aggerritsen/VespaSmartTrap-BASE/docs/hardware/Grove-Vision-AI-Module-V2-functions.jpg

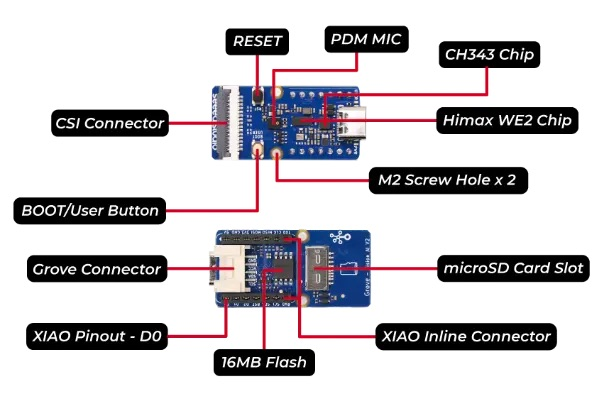
docs/hardware/Grove-Vision-AI-Module-V2-functions.jpg
