aggerritsen/VespaSmartTrap-BASE/tools/data/power_uptime_plot.png

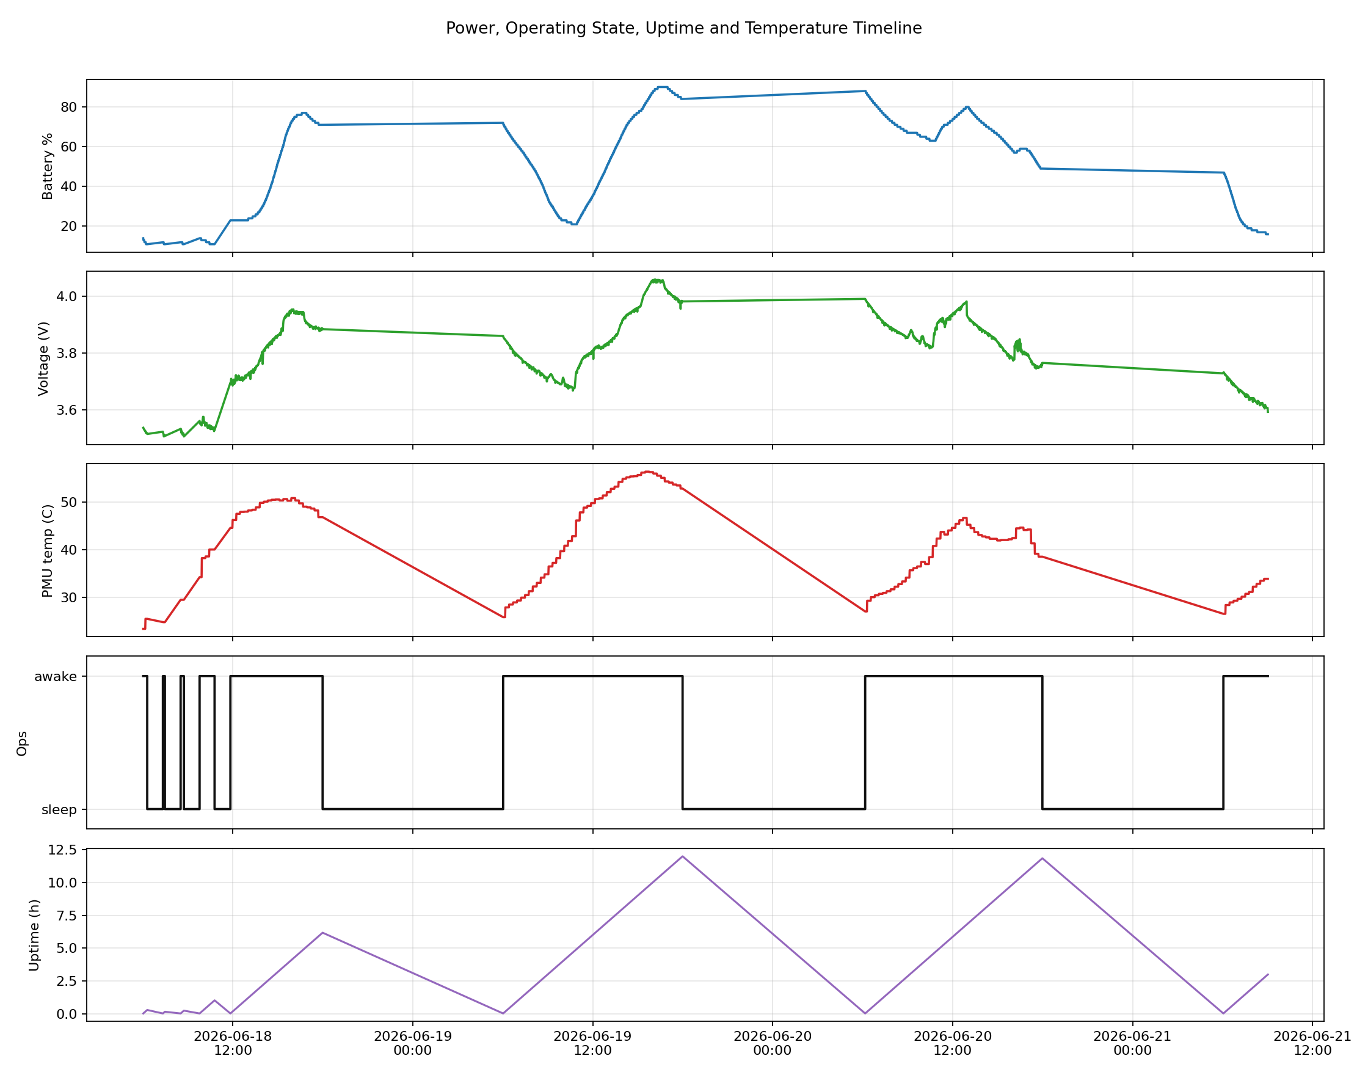
tools/data/power_uptime_plot.png
