aggerritsen/VespaSmartTrap-BASE/tools/image-viewer/images/ApisMellifera/111432916.jpg

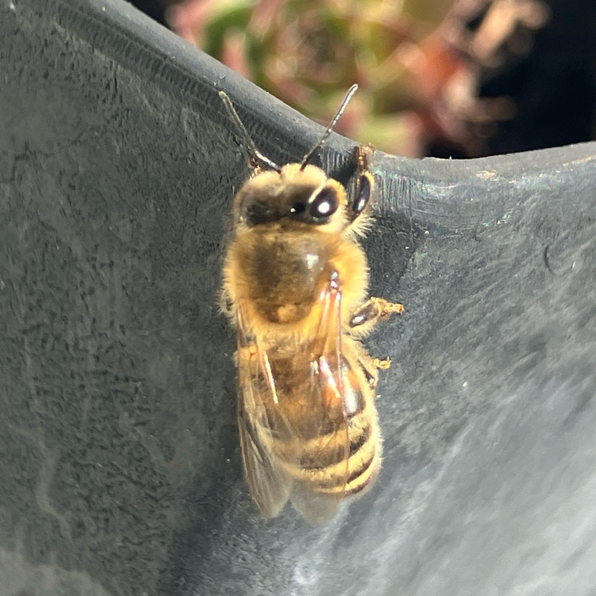
tools/image-viewer/images/ApisMellifera/111432916.jpg
