aggerritsen/VespaSmartTrap-BASE/tools/image-viewer/images/ApisMellifera/111468807.jpg

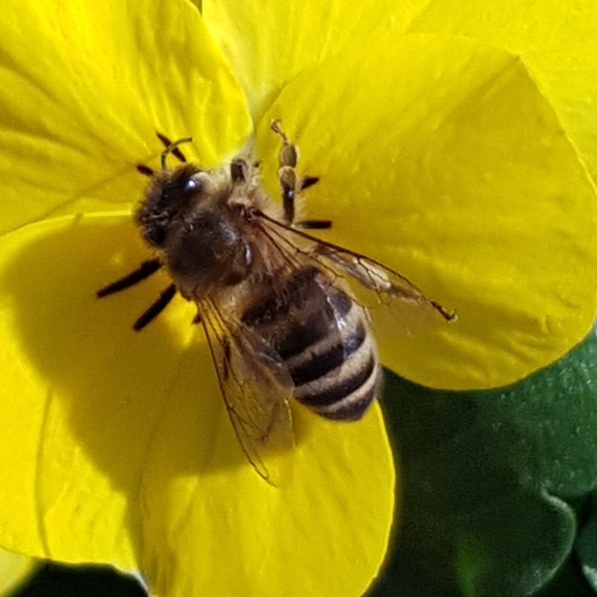
tools/image-viewer/images/ApisMellifera/111468807.jpg
