aggerritsen/VespaSmartTrap-BASE/tools/image-viewer/images/ApisMellifera/111469478.jpg

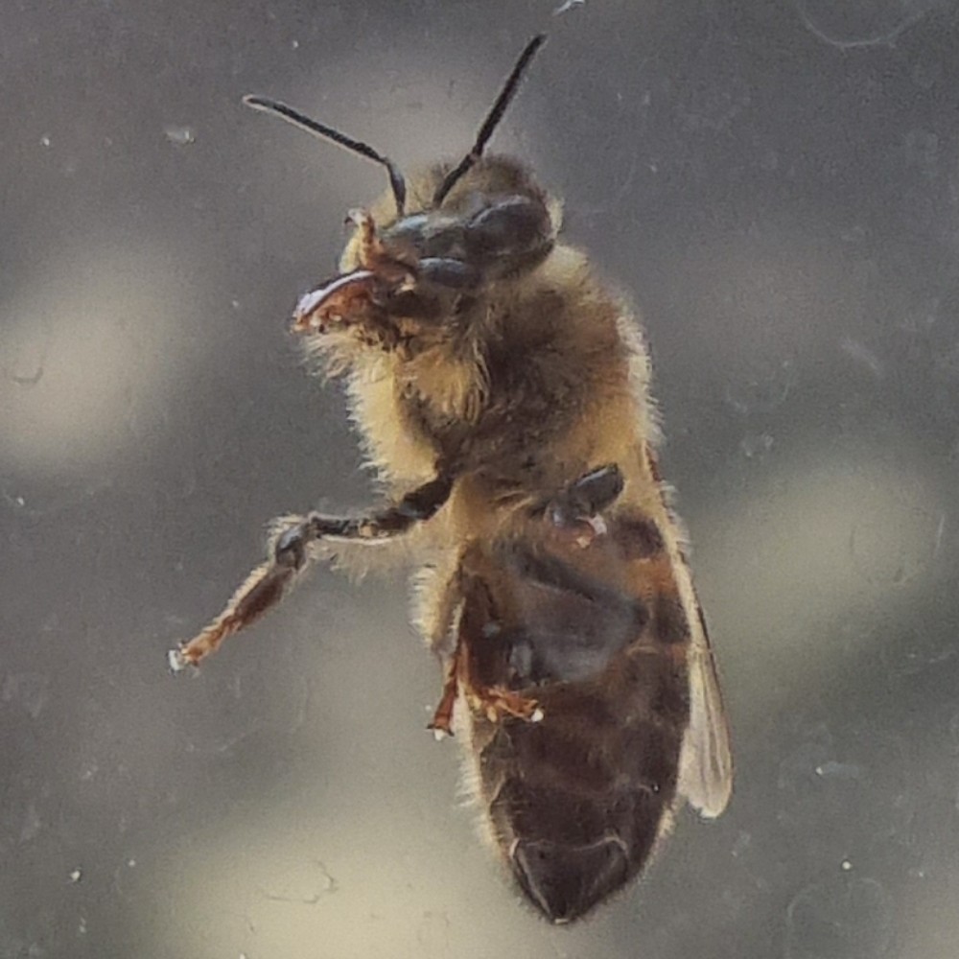
tools/image-viewer/images/ApisMellifera/111469478.jpg
