aggerritsen/VespaSmartTrap-BASE/tools/image-viewer/images/ApisMellifera/111470358.jpg

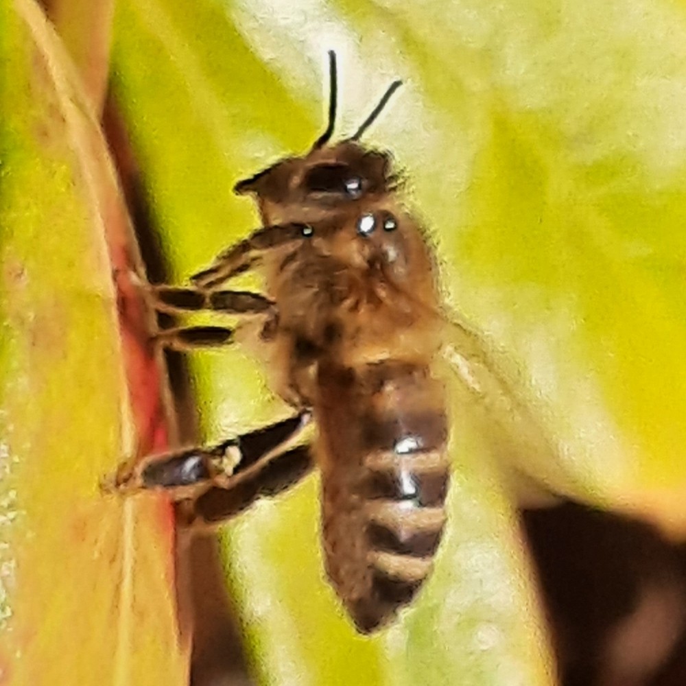
tools/image-viewer/images/ApisMellifera/111470358.jpg
