aggerritsen/VespaSmartTrap-BASE/tools/image-viewer/images/ApisMellifera/111476436.jpg

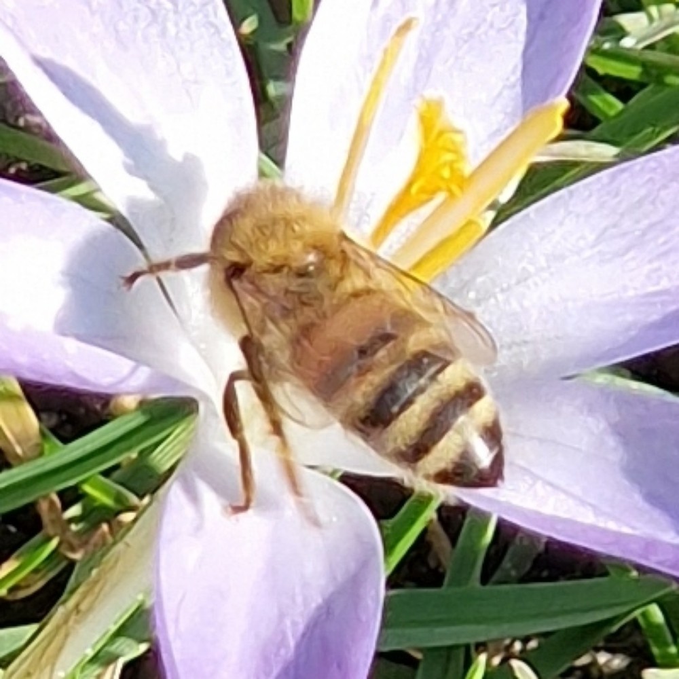
tools/image-viewer/images/ApisMellifera/111476436.jpg
