aggerritsen/VespaSmartTrap-BASE/tools/image-viewer/images/ApisMellifera/111476663.jpg

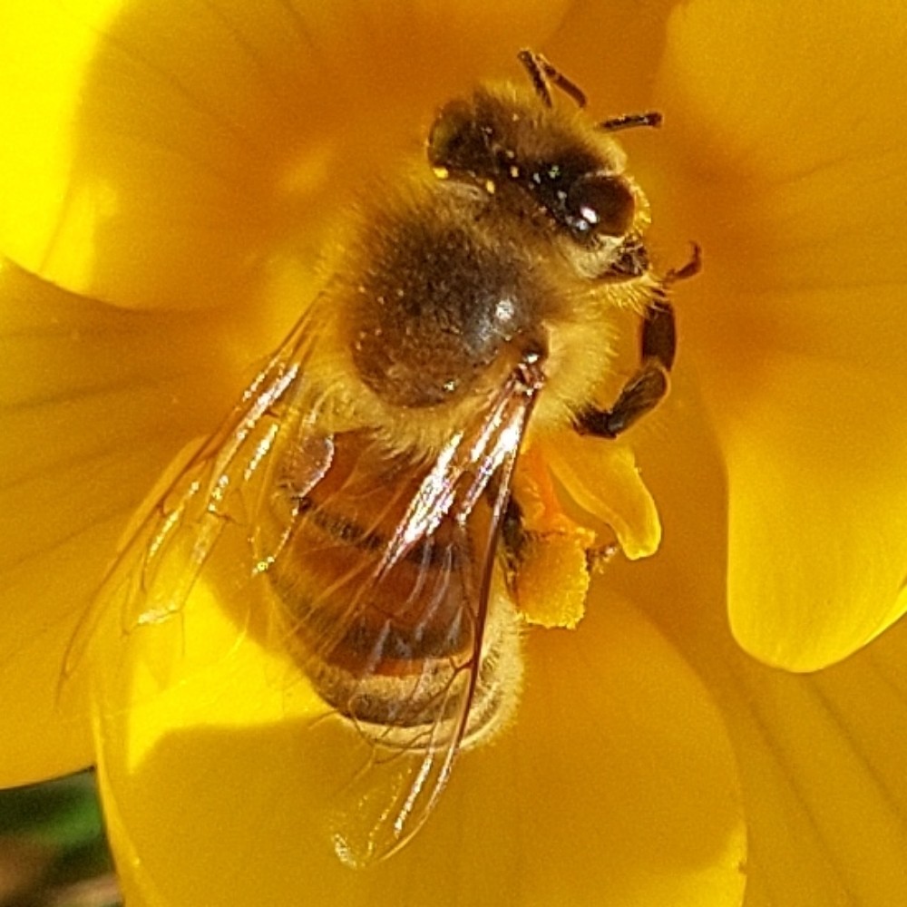
tools/image-viewer/images/ApisMellifera/111476663.jpg
