aggerritsen/VespaSmartTrap-BASE/tools/image-viewer/images/ApisMellifera/111479601.jpg

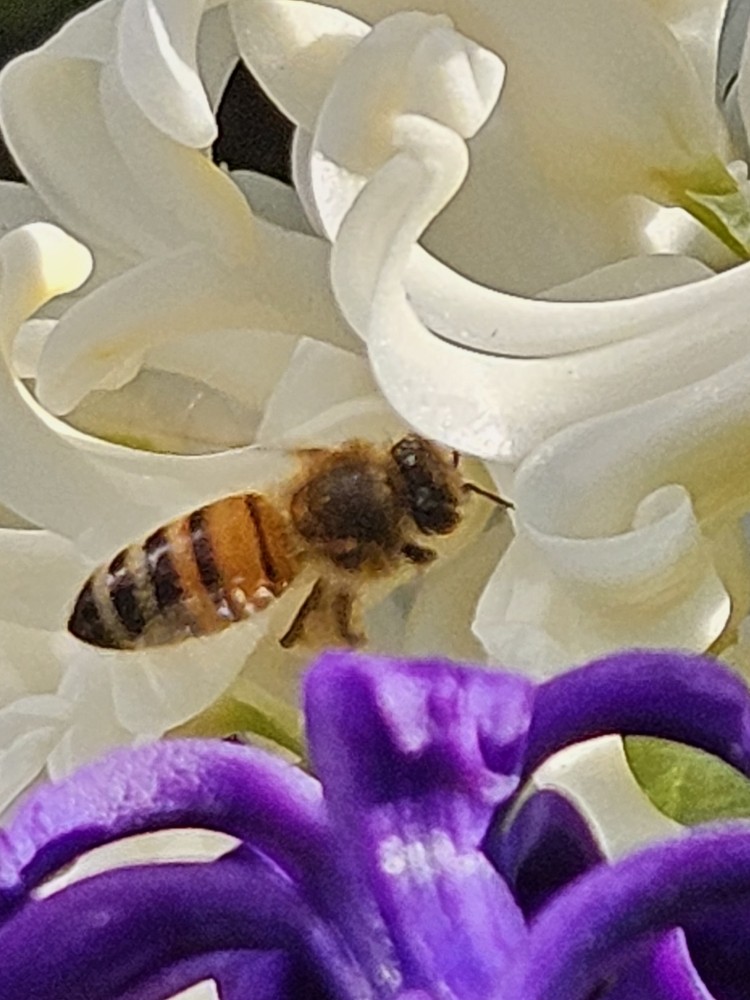
tools/image-viewer/images/ApisMellifera/111479601.jpg
