aggerritsen/VespaSmartTrap-BASE/tools/image-viewer/images/ApisMellifera/111512250.jpg

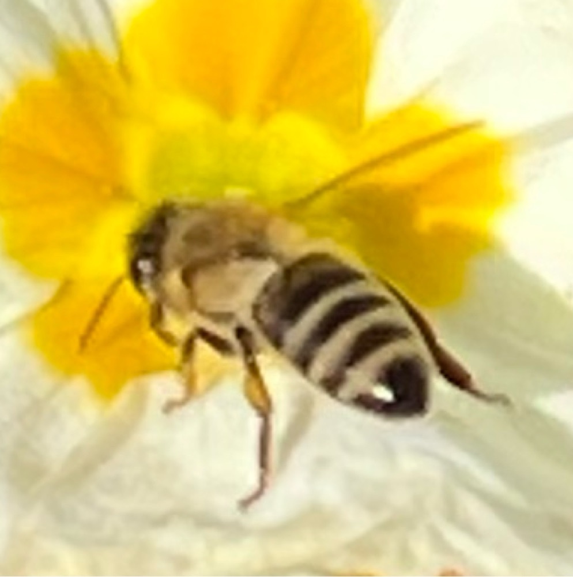
tools/image-viewer/images/ApisMellifera/111512250.jpg
