aggerritsen/VespaSmartTrap-BASE/tools/image-viewer/images/ApisMellifera/111513801.jpg

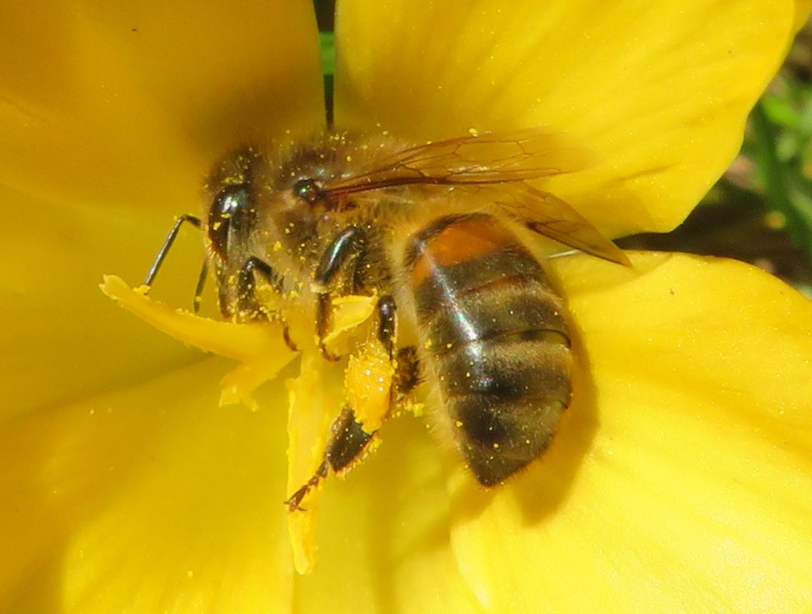
tools/image-viewer/images/ApisMellifera/111513801.jpg
