aggerritsen/VespaSmartTrap-BASE/tools/image-viewer/images/ApisMellifera/112025570.jpg

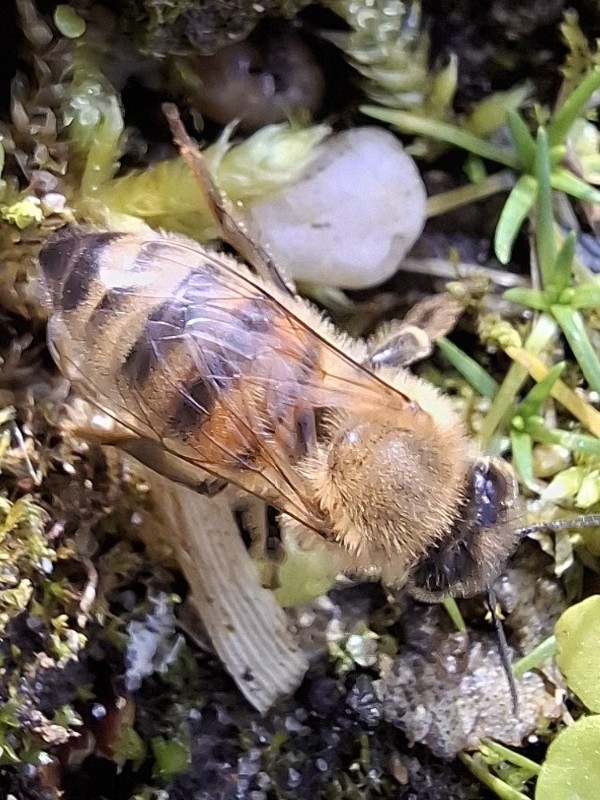
tools/image-viewer/images/ApisMellifera/112025570.jpg
