aggerritsen/VespaSmartTrap-BASE/tools/image-viewer/images/VespaCabro/111761089.jpg

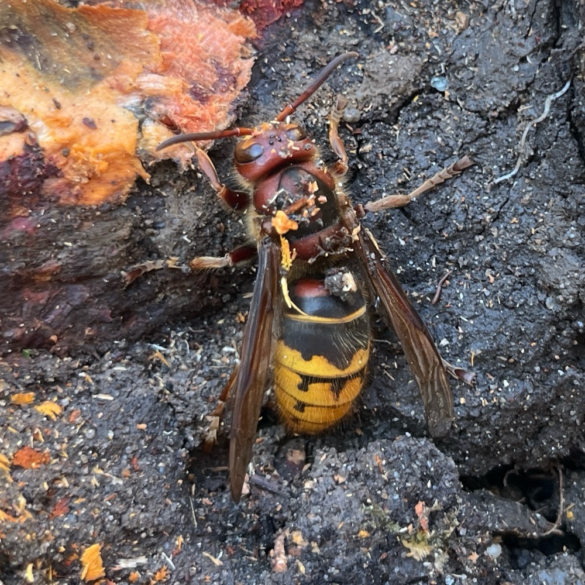
tools/image-viewer/images/VespaCabro/111761089.jpg
