aggerritsen/VespaSmartTrap-BASE/tools/image-viewer/images/VespaCabro/112134146.jpg

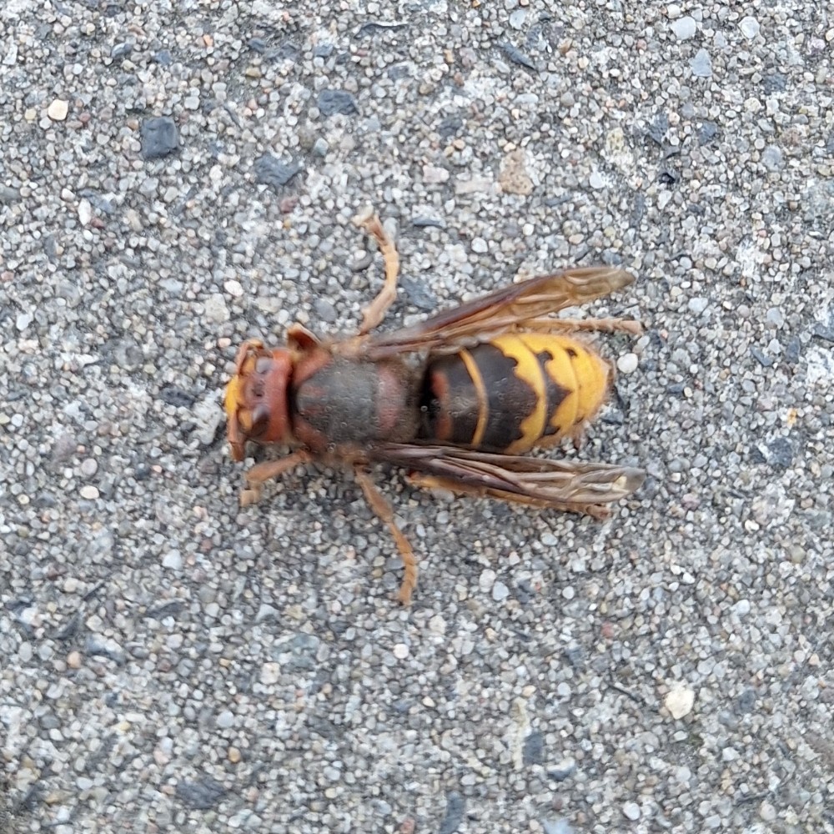
tools/image-viewer/images/VespaCabro/112134146.jpg
