aggerritsen/VespaSmartTrap-BASE/tools/image-viewer/images/VespaCabro/112459961.jpg

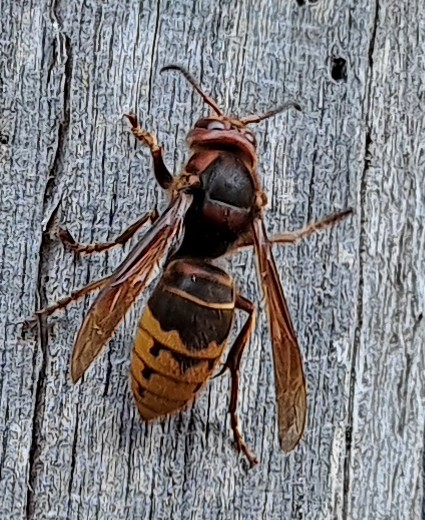
tools/image-viewer/images/VespaCabro/112459961.jpg
