aggerritsen/VespaSmartTrap-BASE/tools/image-viewer/images/VespaCabro/112593887.jpg

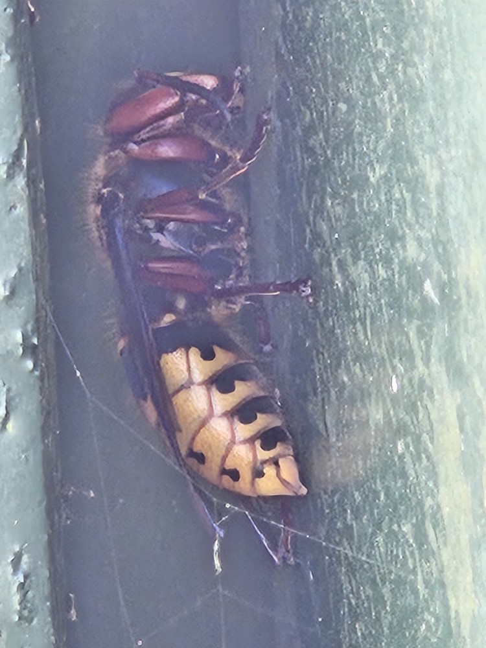
tools/image-viewer/images/VespaCabro/112593887.jpg
