aggerritsen/VespaSmartTrap-BASE/tools/image-viewer/images/VespaCabro/112712739.jpg

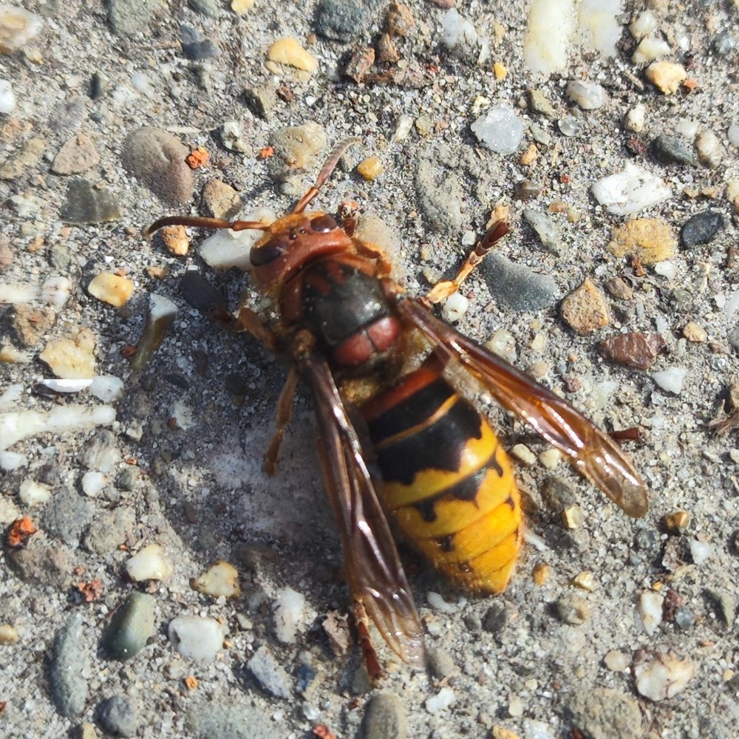
tools/image-viewer/images/VespaCabro/112712739.jpg
