aggerritsen/VespaSmartTrap-BASE/tools/image-viewer/images/VespaCabro/112884580.jpg

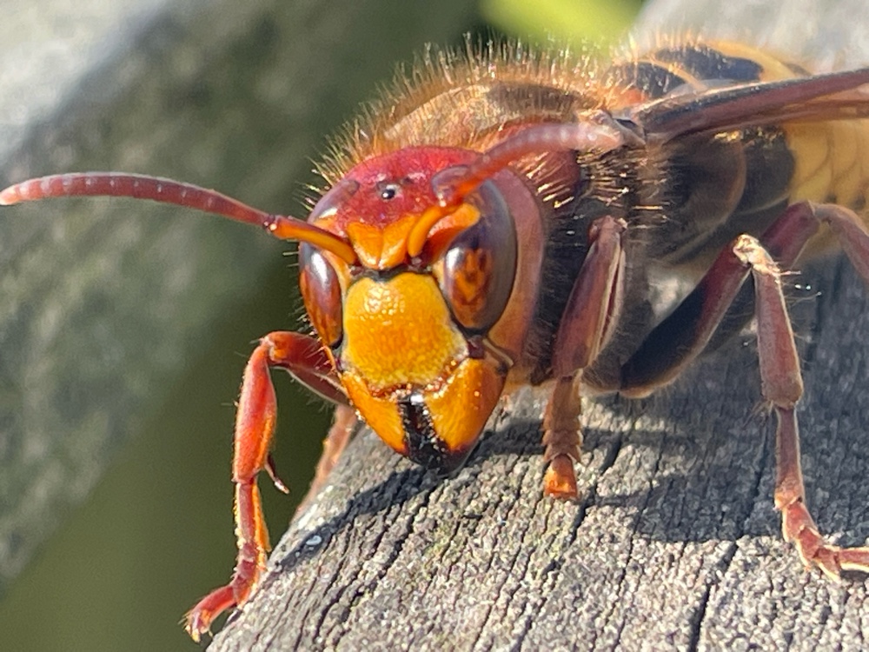
tools/image-viewer/images/VespaCabro/112884580.jpg
