aggerritsen/VespaSmartTrap-BASE/tools/image-viewer/images/VespaCabro/112900468.jpg

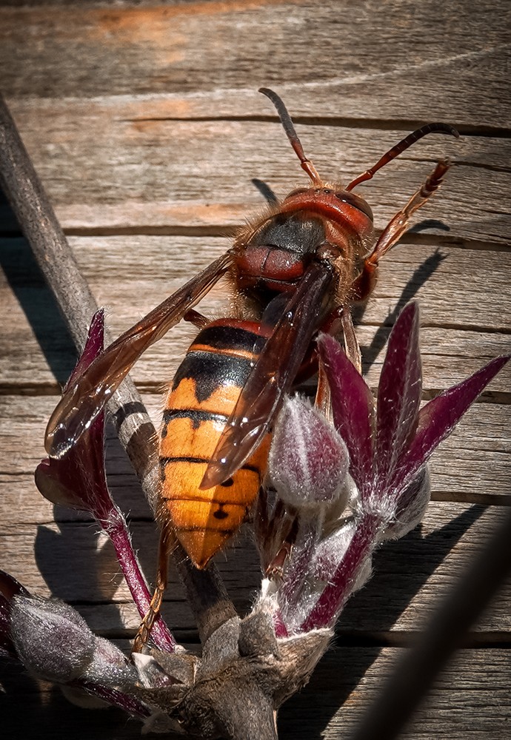
tools/image-viewer/images/VespaCabro/112900468.jpg
