aggerritsen/VespaSmartTrap-BASE/tools/image-viewer/images/VespaCabro/112967960.jpg

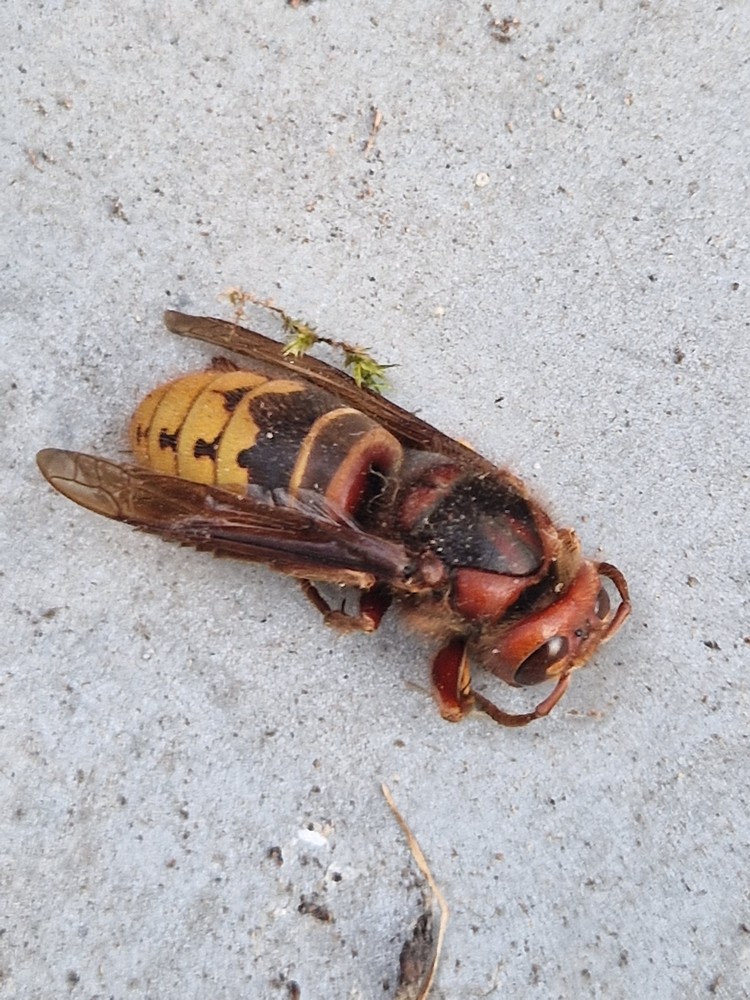
tools/image-viewer/images/VespaCabro/112967960.jpg
