aggerritsen/VespaSmartTrap-BASE/tools/image-viewer/images/VespaCabro/113068991.jpg

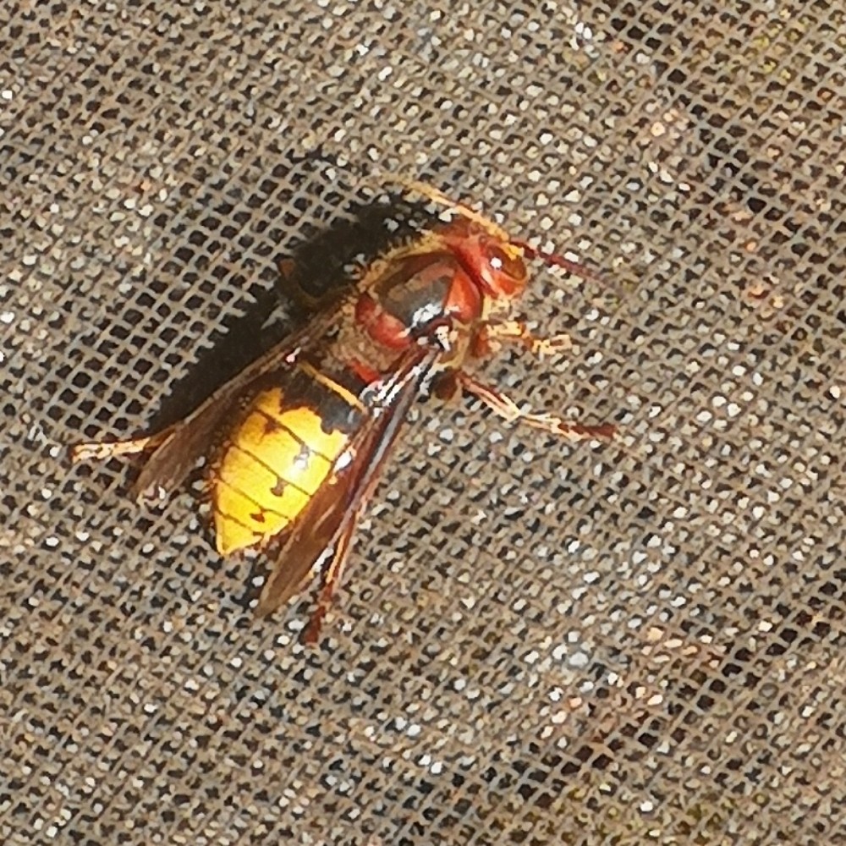
tools/image-viewer/images/VespaCabro/113068991.jpg
