aggerritsen/VespaSmartTrap-BASE/tools/image-viewer/images/VespaVelutina/112178689.jpg

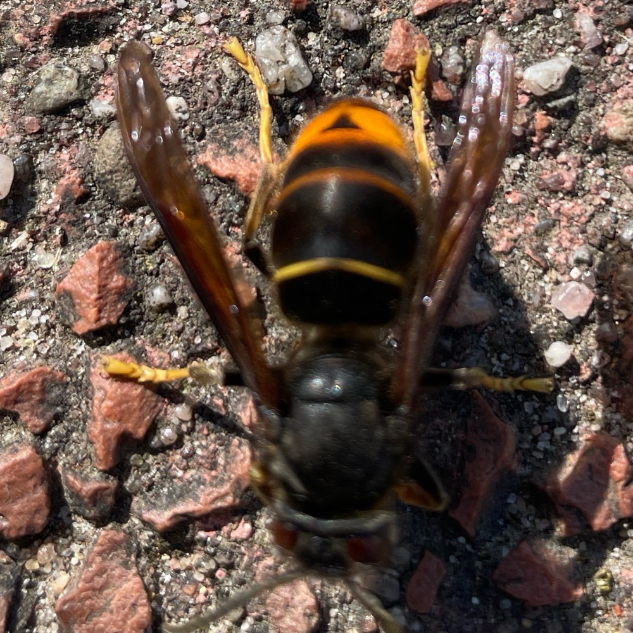
tools/image-viewer/images/VespaVelutina/112178689.jpg
