aggerritsen/VespaSmartTrap-BASE/tools/image-viewer/images/VespaVelutina/112180438.jpg

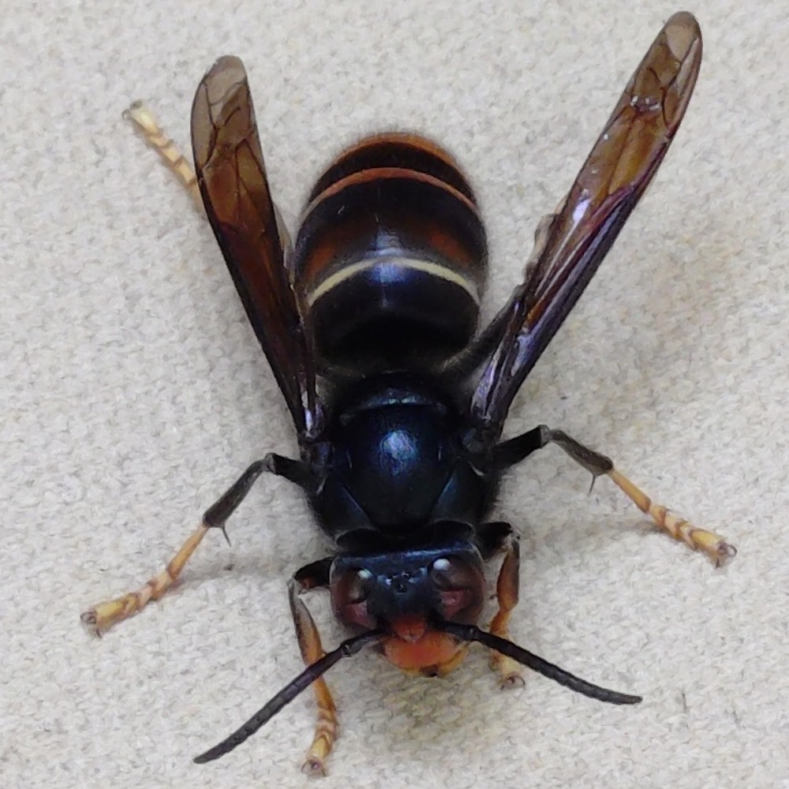
tools/image-viewer/images/VespaVelutina/112180438.jpg
