aggerritsen/VespaSmartTrap-BASE/tools/image-viewer/images/VespaVelutina/112218984.jpg

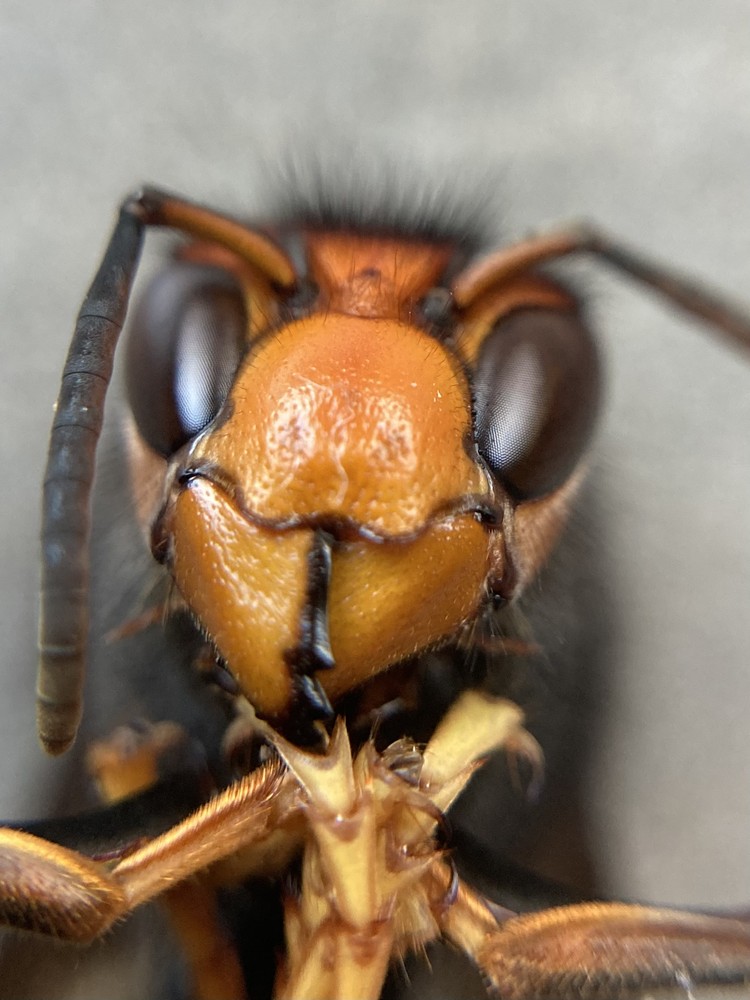
tools/image-viewer/images/VespaVelutina/112218984.jpg
