aggerritsen/VespaSmartTrap-BASE/tools/image-viewer/images/VespaVelutina/112255665.jpg

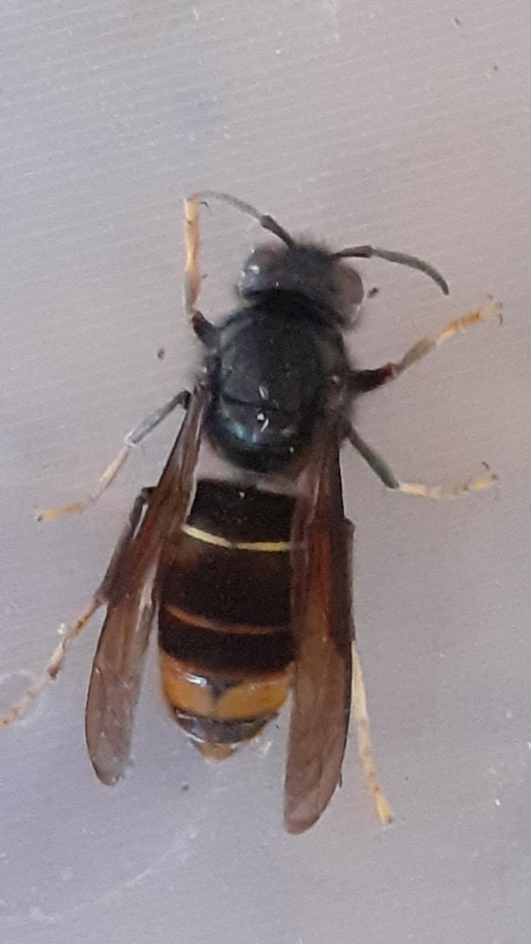
tools/image-viewer/images/VespaVelutina/112255665.jpg
