aggerritsen/VespaSmartTrap-BASE/tools/image-viewer/images/VespaVelutina/113046975.jpg

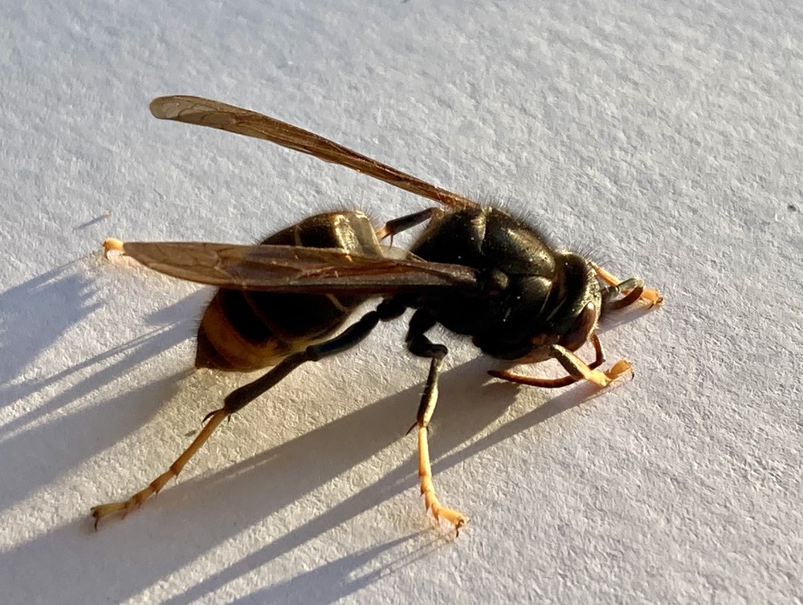
tools/image-viewer/images/VespaVelutina/113046975.jpg
