aggerritsen/VespaSmartTrap-BASE/tools/image-viewer/images/VespaVelutina/113052811.jpg

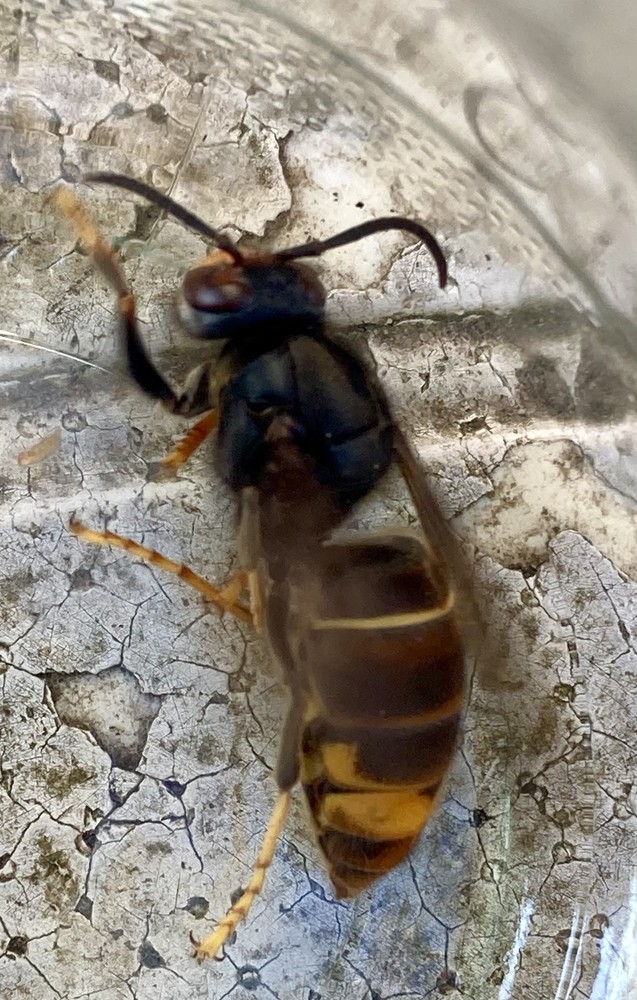
tools/image-viewer/images/VespaVelutina/113052811.jpg
