aggerritsen/VespaSmartTrap-BASE/tools/image-viewer/images/VespaVelutina/113054008.jpg

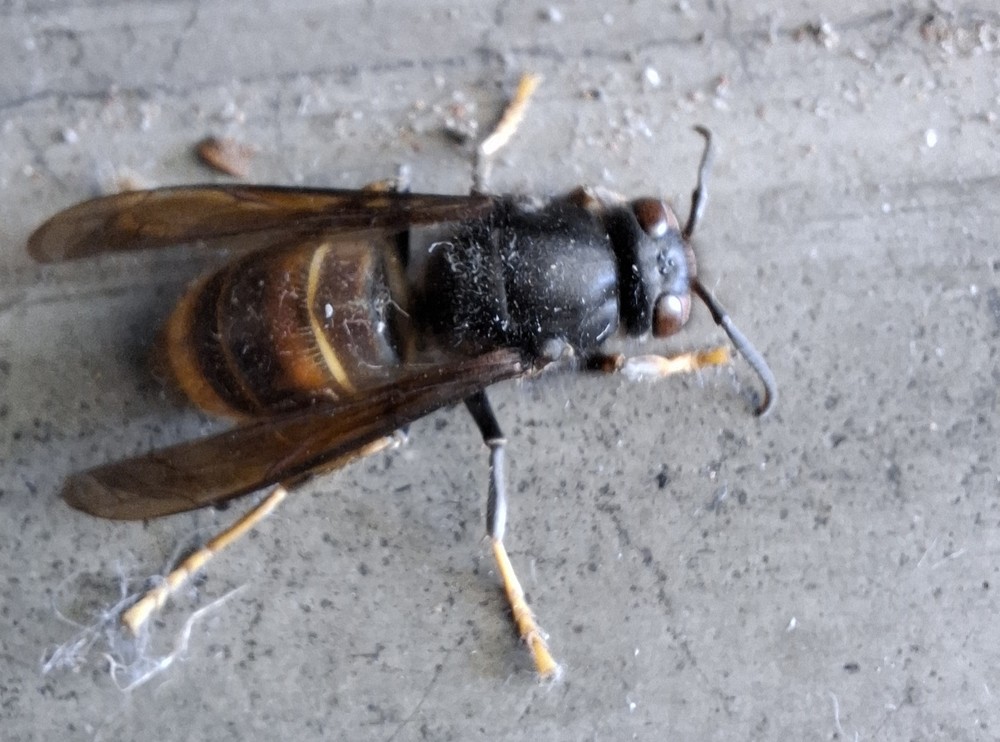
tools/image-viewer/images/VespaVelutina/113054008.jpg
