aggerritsen/VespaSmartTrap-BASE/tools/image-viewer/images/VespaVelutina/113058650.jpg

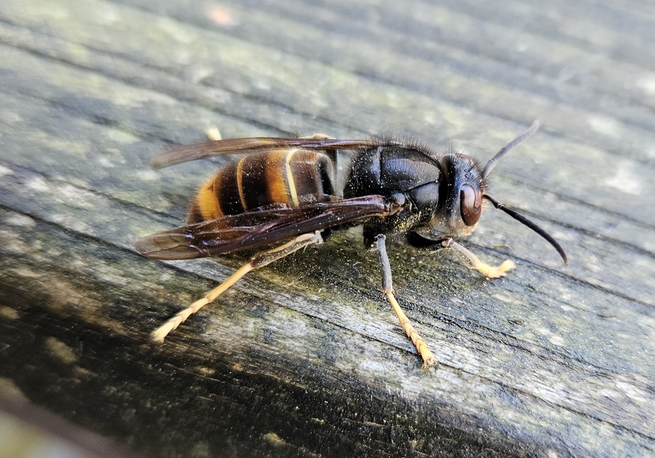
tools/image-viewer/images/VespaVelutina/113058650.jpg
