aggerritsen/VespaSmartTrap-BASE/tools/image-viewer/images/VespaVelutina/113204112.jpg

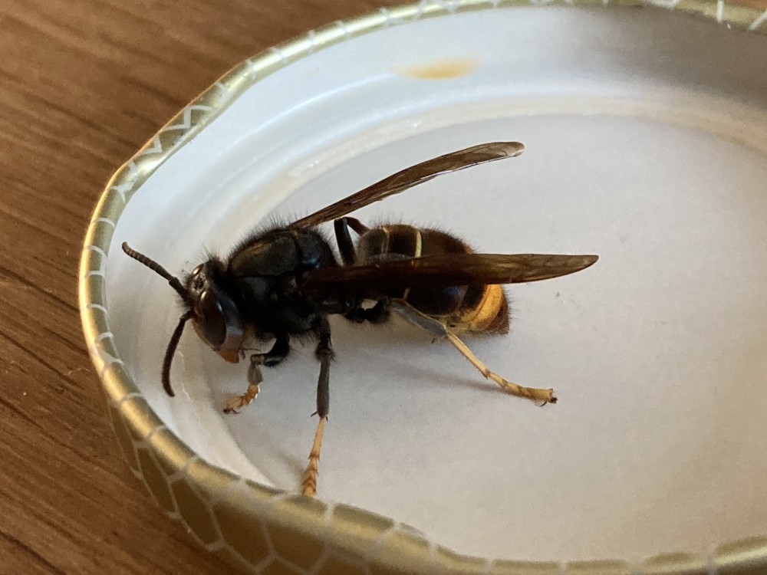
tools/image-viewer/images/VespaVelutina/113204112.jpg
