aggerritsen/VespaSmartTrap-BASE/tools/image-viewer/images/VespaVelutina/113204113.jpg

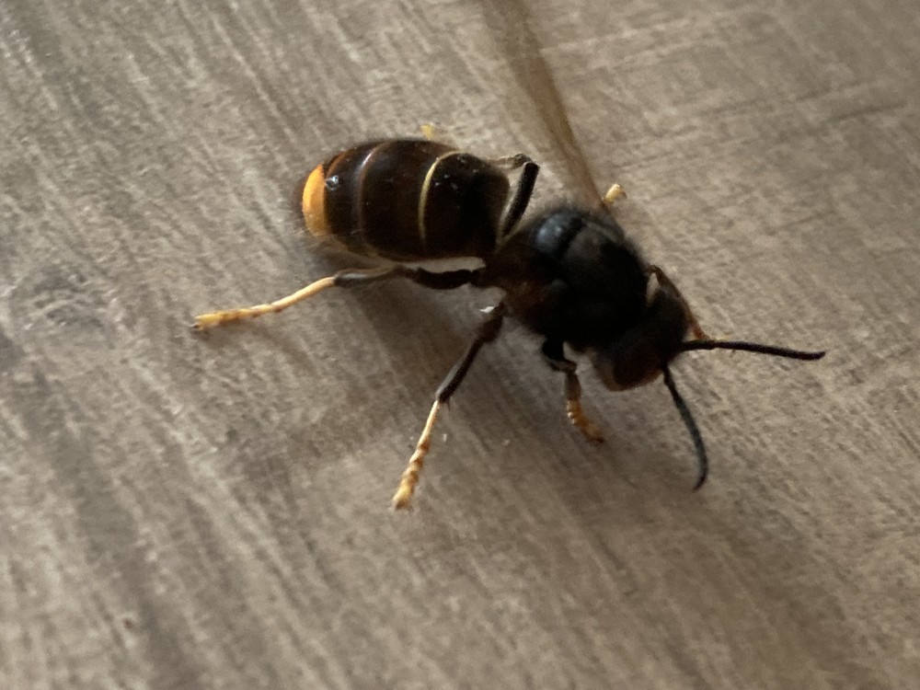
tools/image-viewer/images/VespaVelutina/113204113.jpg
