aggerritsen/VespaSmartTrap-BASE/tools/image-viewer/images/VespaVelutina/141795838.jpg

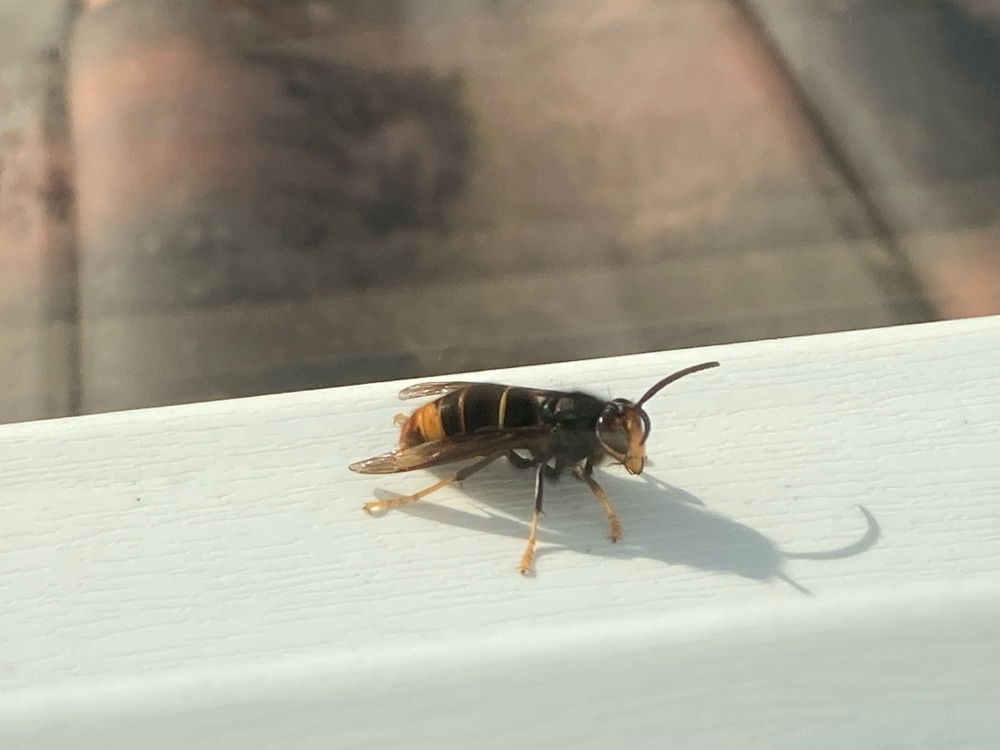
tools/image-viewer/images/VespaVelutina/141795838.jpg
