aggerritsen/VespaSmartTrap-BASE/tools/image-viewer/images/VespaVelutina/141813378.jpg

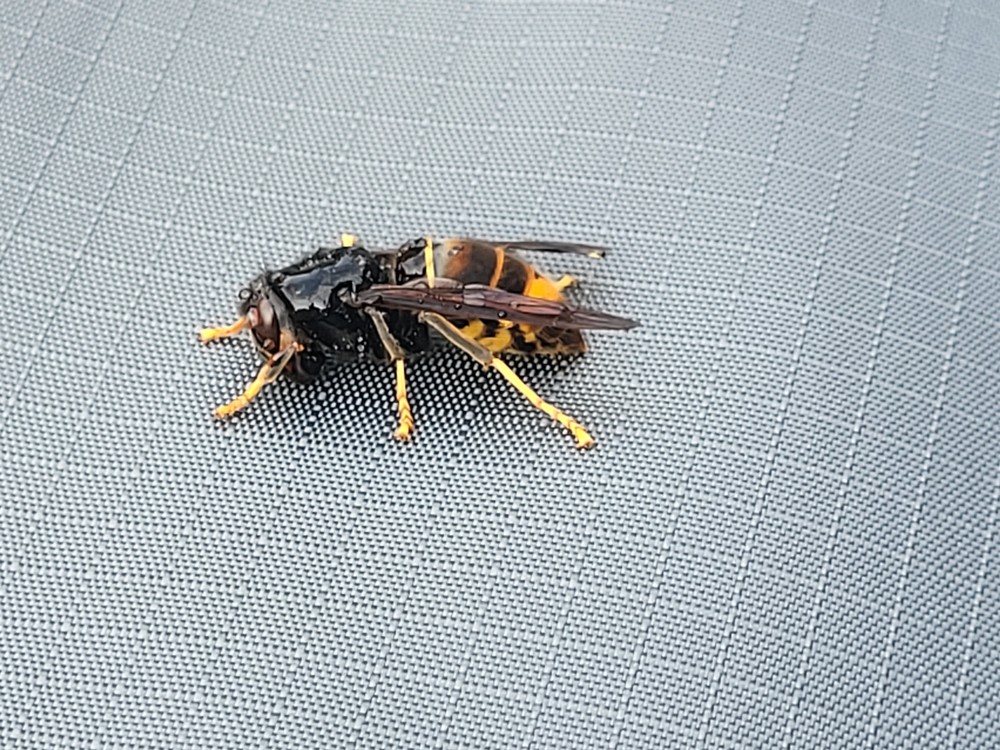
tools/image-viewer/images/VespaVelutina/141813378.jpg
