aggerritsen/VespaSmartTrap-BASE/tools/image-viewer/images/VespaVelutina/141822580 (1).jpg

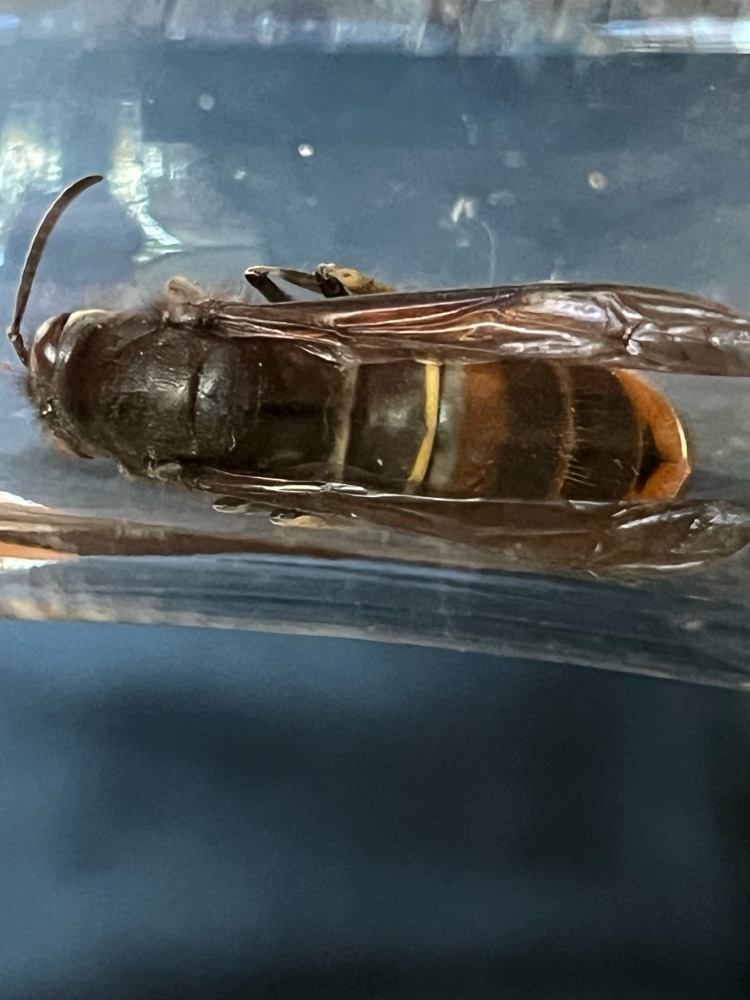
tools/image-viewer/images/VespaVelutina/141822580 (1).jpg
