aggerritsen/VespaSmartTrap-BASE/tools/image-viewer/images/VespaVelutina/141822581.jpg

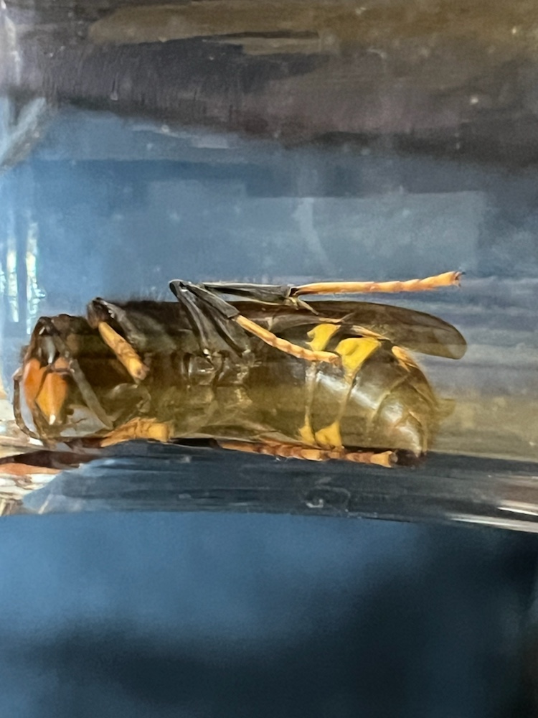
tools/image-viewer/images/VespaVelutina/141822581.jpg
