aggerritsen/VespaSmartTrap-BASE/tools/image-viewer/images/VespaVelutina/141857367.jpg

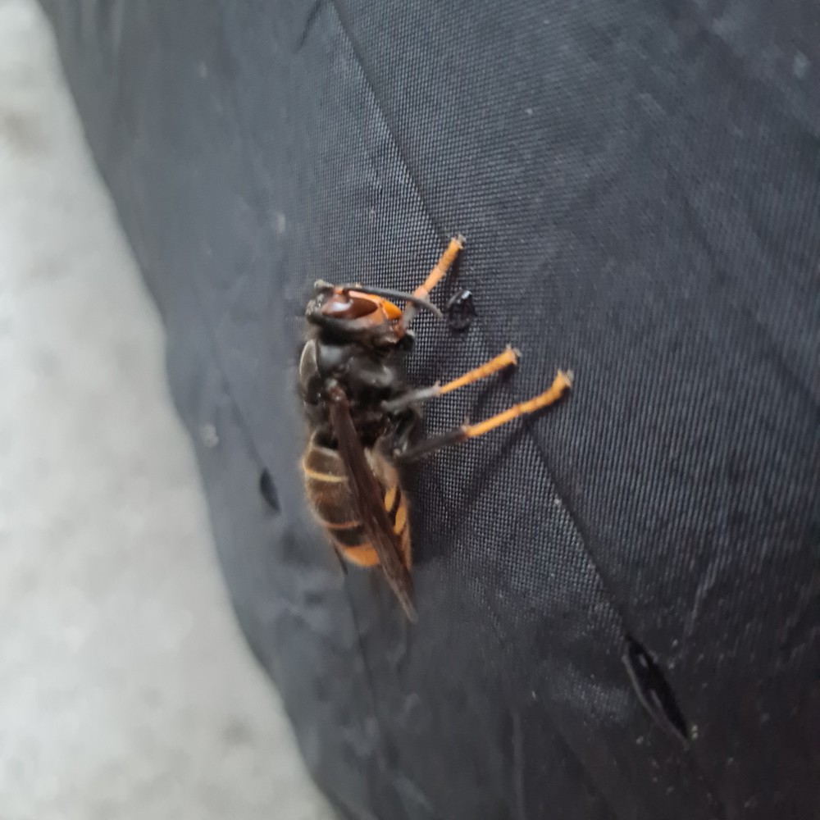
tools/image-viewer/images/VespaVelutina/141857367.jpg
