aggerritsen/VespaSmartTrap-BASE/tools/image-viewer/images/VespaVelutina/141879811.jpg

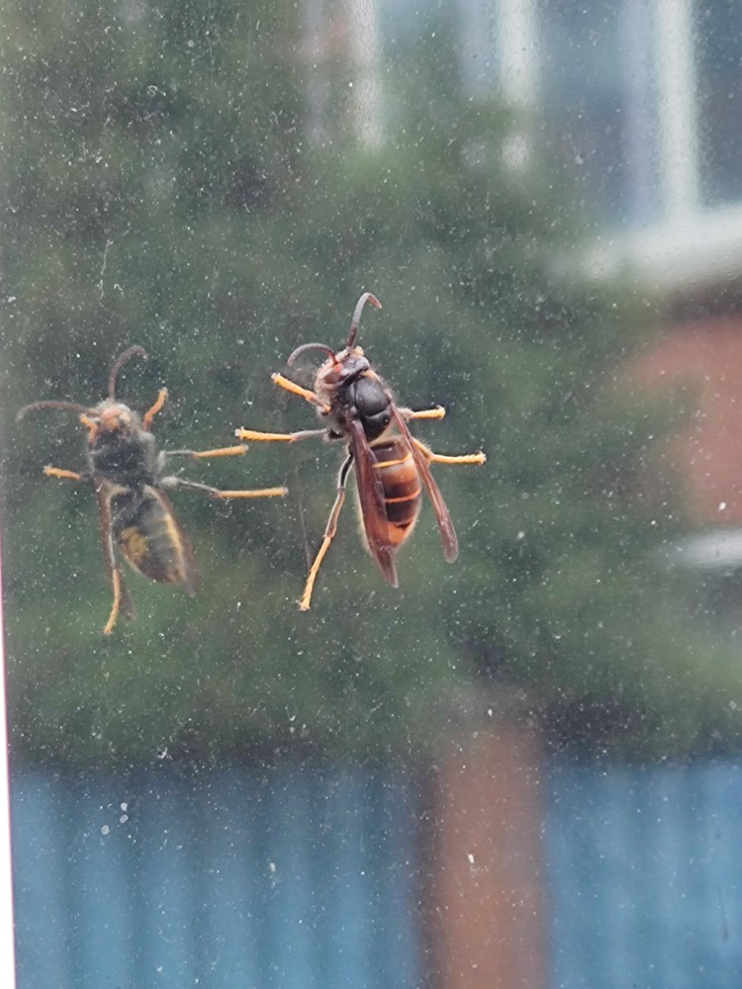
tools/image-viewer/images/VespaVelutina/141879811.jpg
