aggerritsen/VespaSmartTrap-BASE/tools/image-viewer/images/VespaVelutina/141879851 (1).jpg

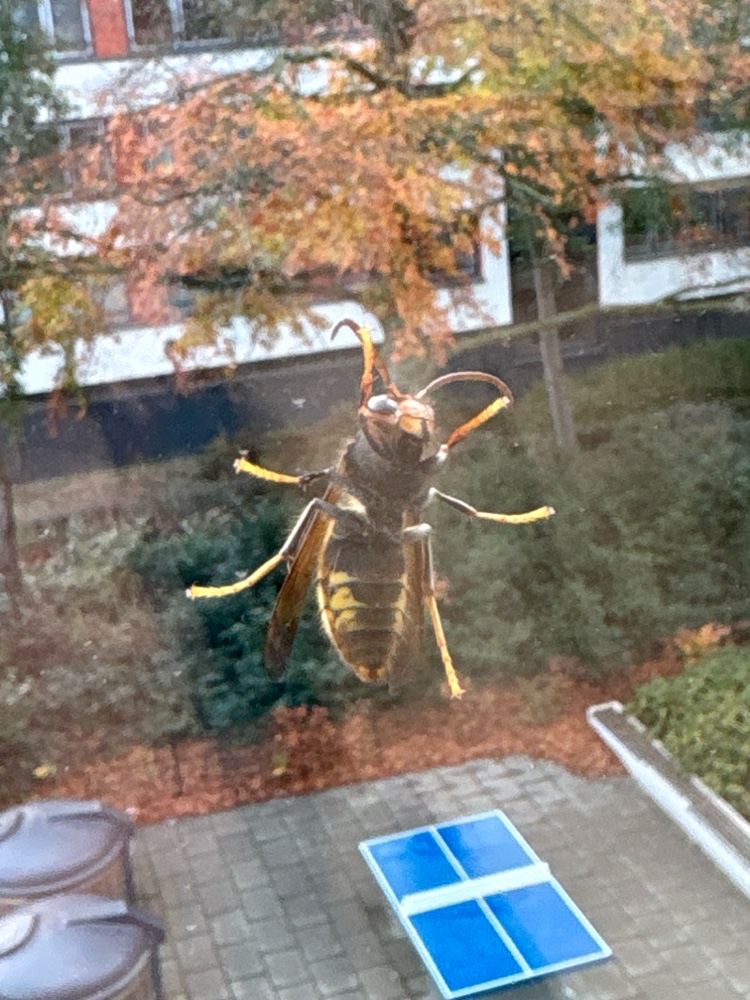
tools/image-viewer/images/VespaVelutina/141879851 (1).jpg
