aggerritsen/VespaSmartTrap-BASE/tools/image-viewer/images/VespaVelutina/141898289.jpg

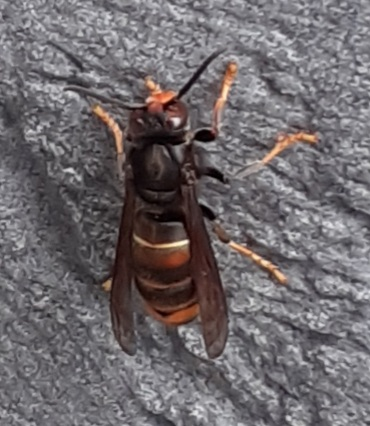
tools/image-viewer/images/VespaVelutina/141898289.jpg
