aggerritsen/VespaSmartTrap-BASE/tools/image-viewer/images/VespaVelutina/141899238.jpg

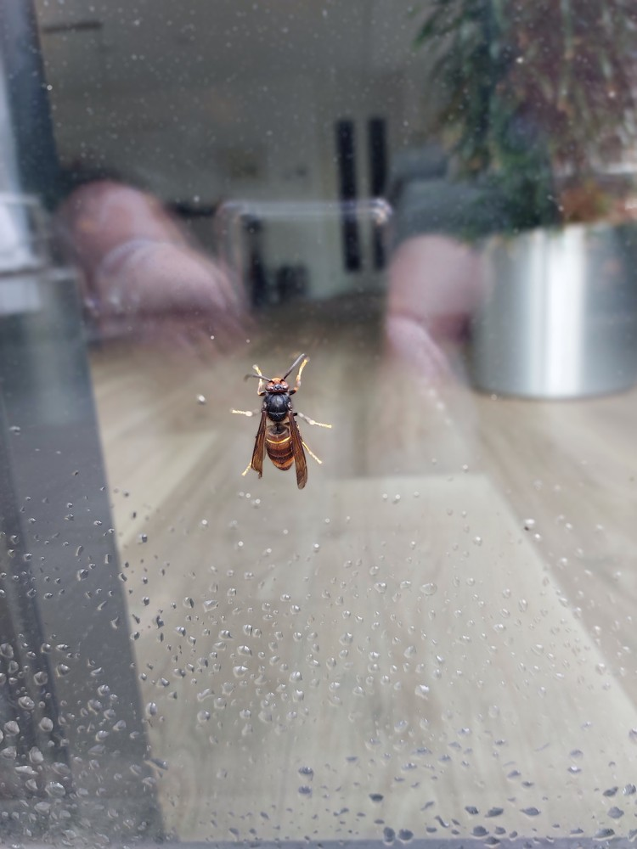
tools/image-viewer/images/VespaVelutina/141899238.jpg
