aggerritsen/VespaSmartTrap-BASE/tools/image-viewer/images/VespaVelutina/141922662.jpg

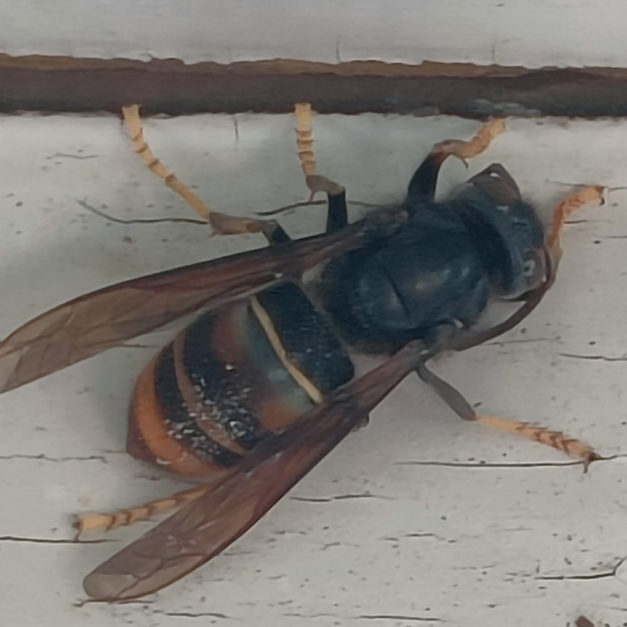
tools/image-viewer/images/VespaVelutina/141922662.jpg
