aggerritsen/VespaSmartTrap-BASE/tools/image-viewer/images/VespaVelutina/141945183.jpg

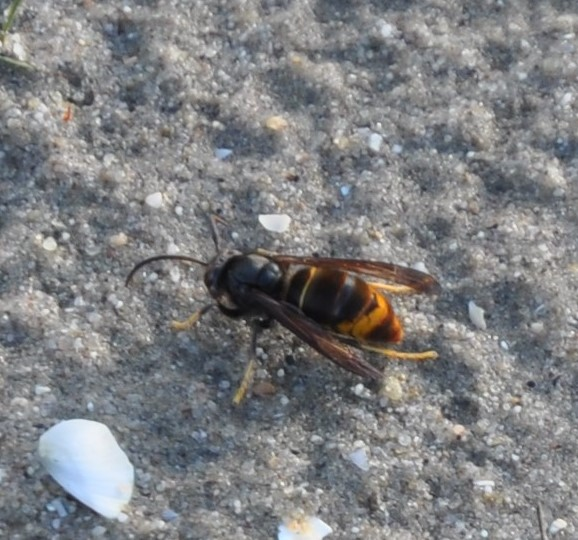
tools/image-viewer/images/VespaVelutina/141945183.jpg
