aggerritsen/VespaSmartTrap-BASE/tools/image-viewer/images/VespaVelutina/141958314.jpg

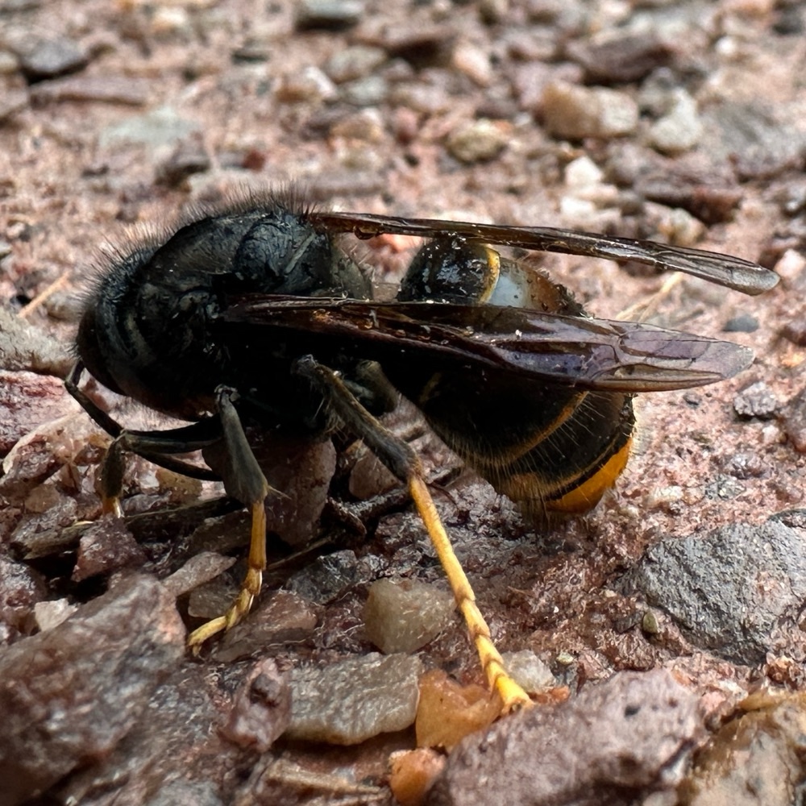
tools/image-viewer/images/VespaVelutina/141958314.jpg
