aggerritsen/VespaSmartTrap-BASE/tools/image-viewer/images/VespaVelutina/142006424.jpg

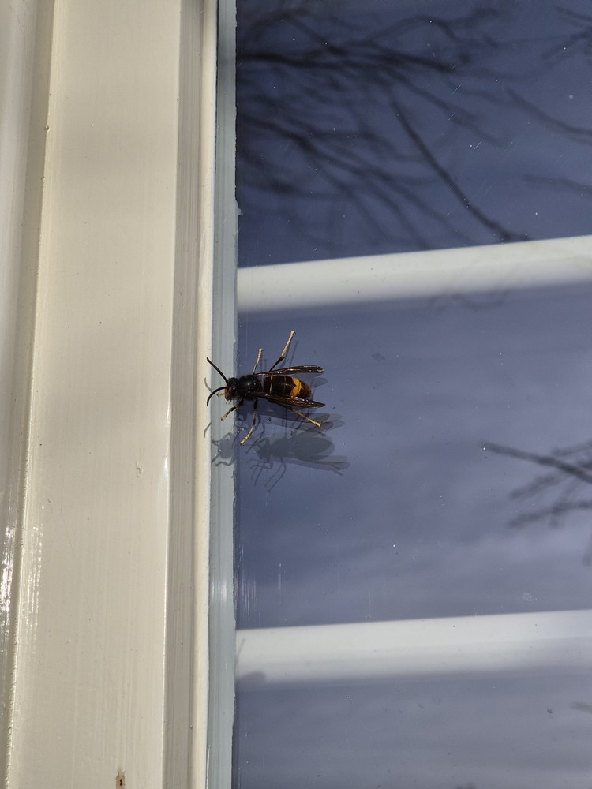
tools/image-viewer/images/VespaVelutina/142006424.jpg
