aggerritsen/VespaSmartTrap-BASE/tools/image-viewer/images/VespaVelutina/142009313.jpg

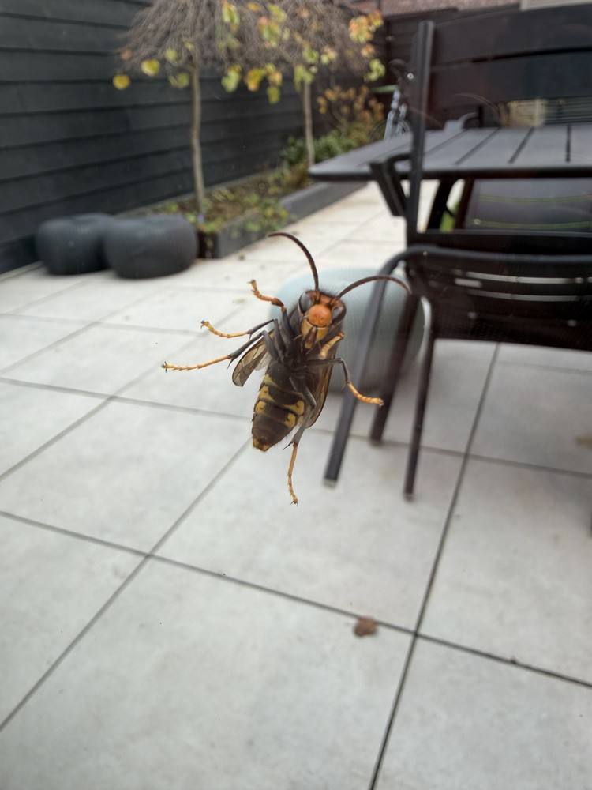
tools/image-viewer/images/VespaVelutina/142009313.jpg
