aggerritsen/VespaSmartTrap-BASE/tools/image-viewer/images/VespaVelutina/142023775.jpg

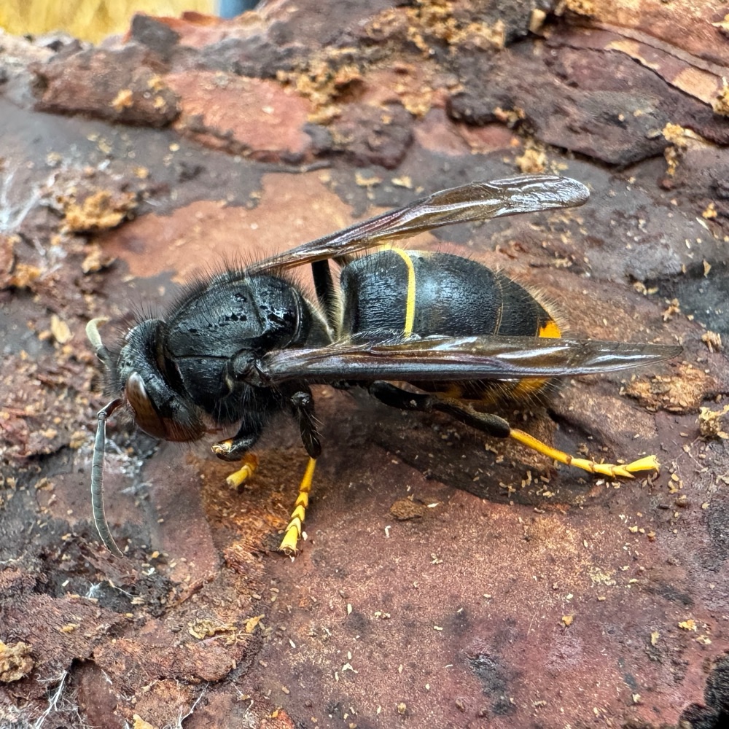
tools/image-viewer/images/VespaVelutina/142023775.jpg
