aggerritsen/VespaSmartTrap-BASE/tools/image-viewer/images/VespaVelutina/142036786.jpg

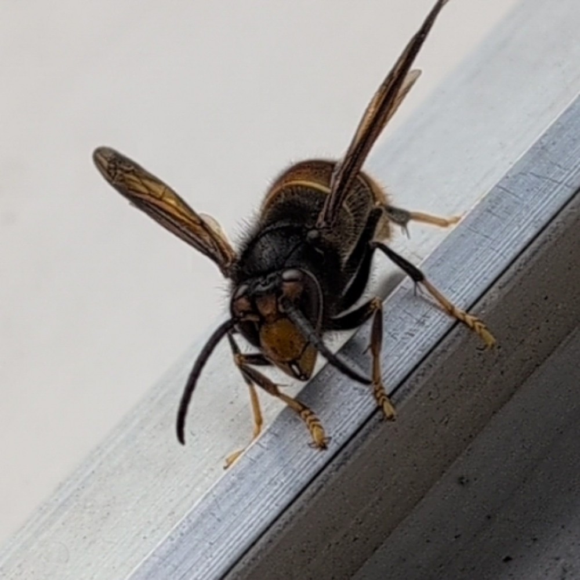
tools/image-viewer/images/VespaVelutina/142036786.jpg
