aggerritsen/VespaSmartTrap-BASE/tools/image-viewer/images/VespaVelutina/142039438.jpg

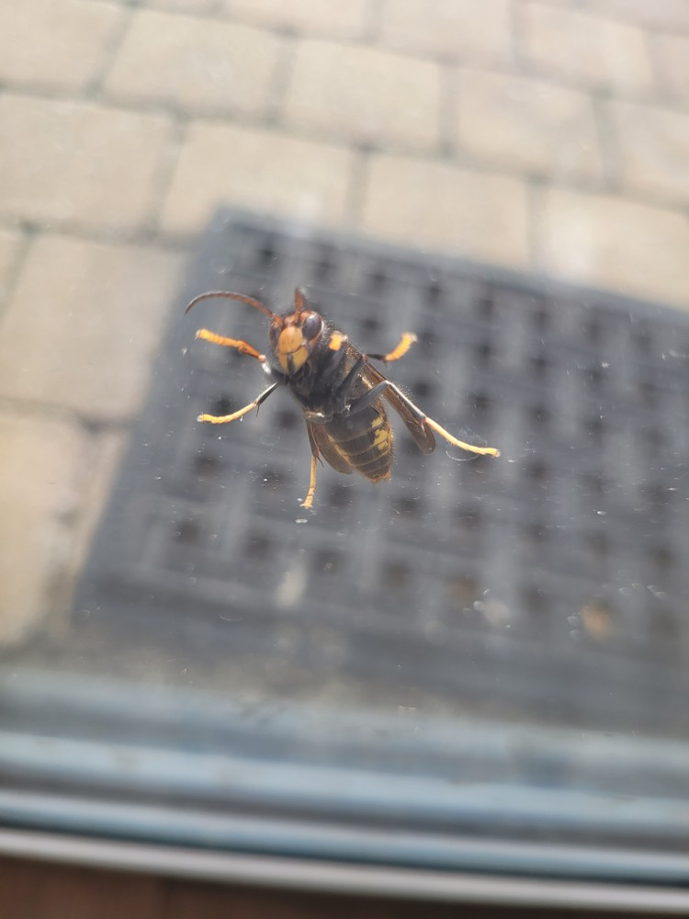
tools/image-viewer/images/VespaVelutina/142039438.jpg
