aggerritsen/VespaSmartTrap-BASE/tools/image-viewer/images/VespaVelutina/142039439.jpg

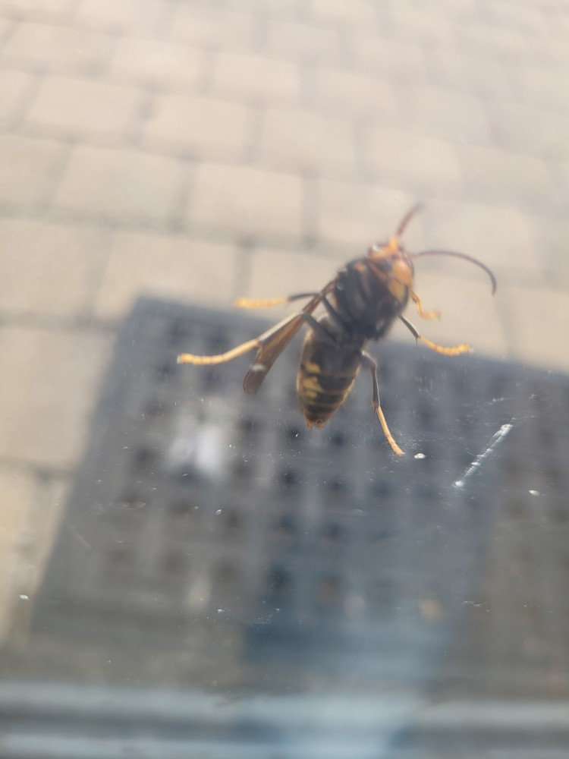
tools/image-viewer/images/VespaVelutina/142039439.jpg
