aggerritsen/VespaSmartTrap-BASE/tools/image-viewer/images/VespaVelutina/142063808.jpg

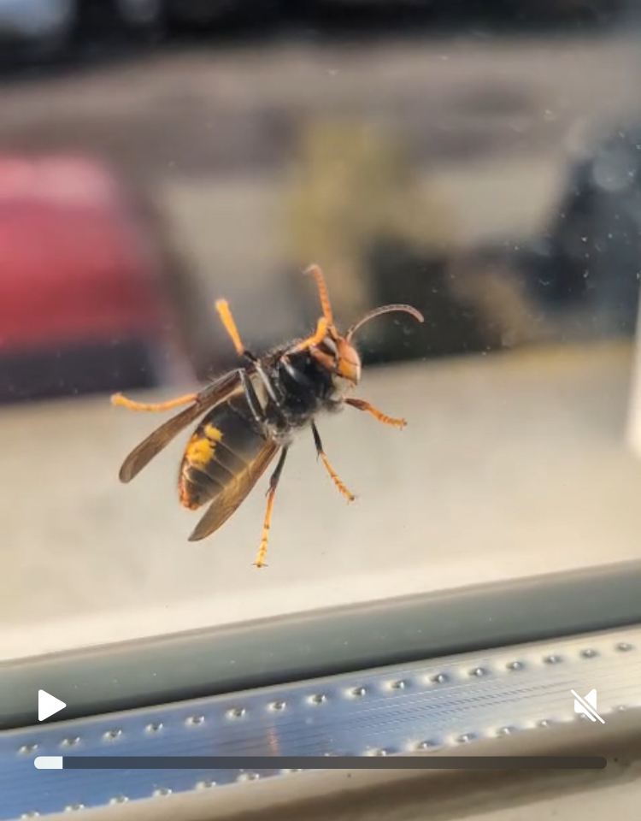
tools/image-viewer/images/VespaVelutina/142063808.jpg
