aggerritsen/VespaSmartTrap-BASE/tools/image-viewer/images/VespaVelutina/142083147.jpg

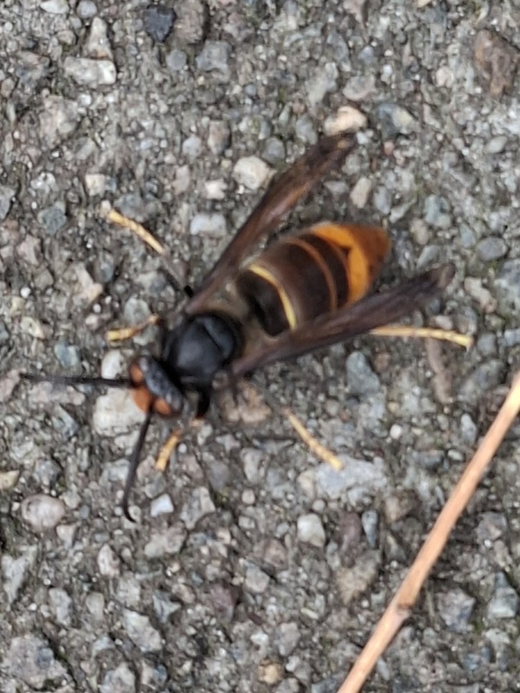
tools/image-viewer/images/VespaVelutina/142083147.jpg
