aggerritsen/VespaSmartTrap-BASE/tools/image-viewer/images/VespaVelutina/142120125.jpg

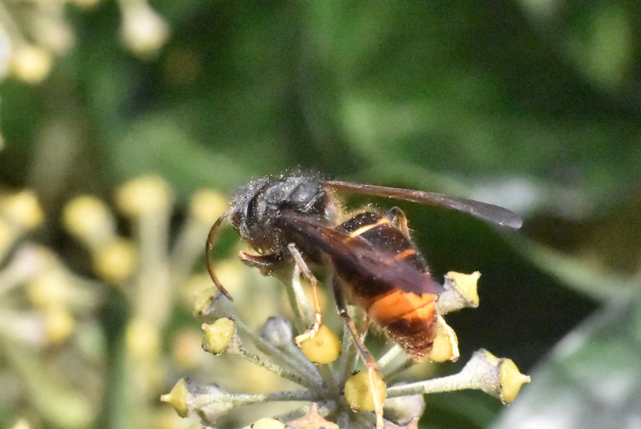
tools/image-viewer/images/VespaVelutina/142120125.jpg
