aggerritsen/VespaSmartTrap-BASE/tools/image-viewer/images/VespaVelutina/142154816.jpg

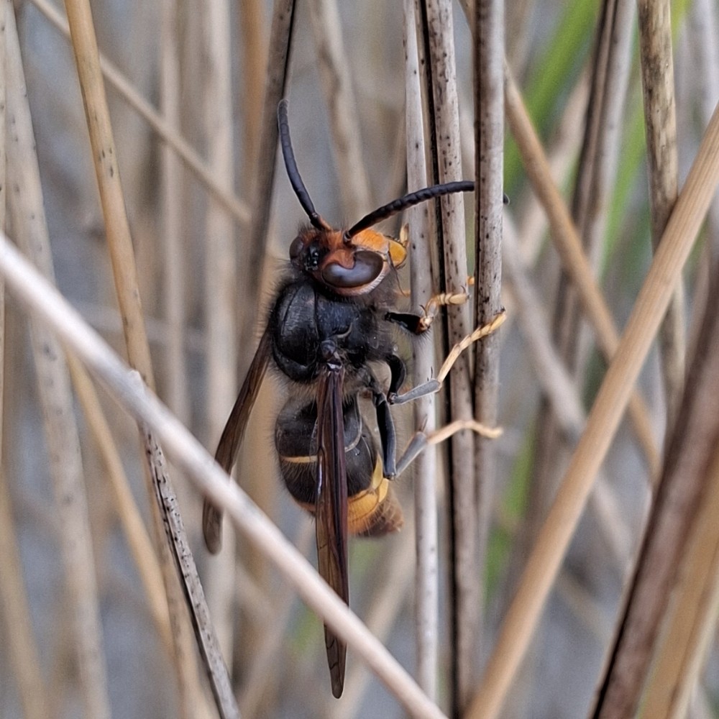
tools/image-viewer/images/VespaVelutina/142154816.jpg
