aggerritsen/VespaSmartTrap-BASE/tools/image-viewer/images/VespaVelutina/142253273.jpg

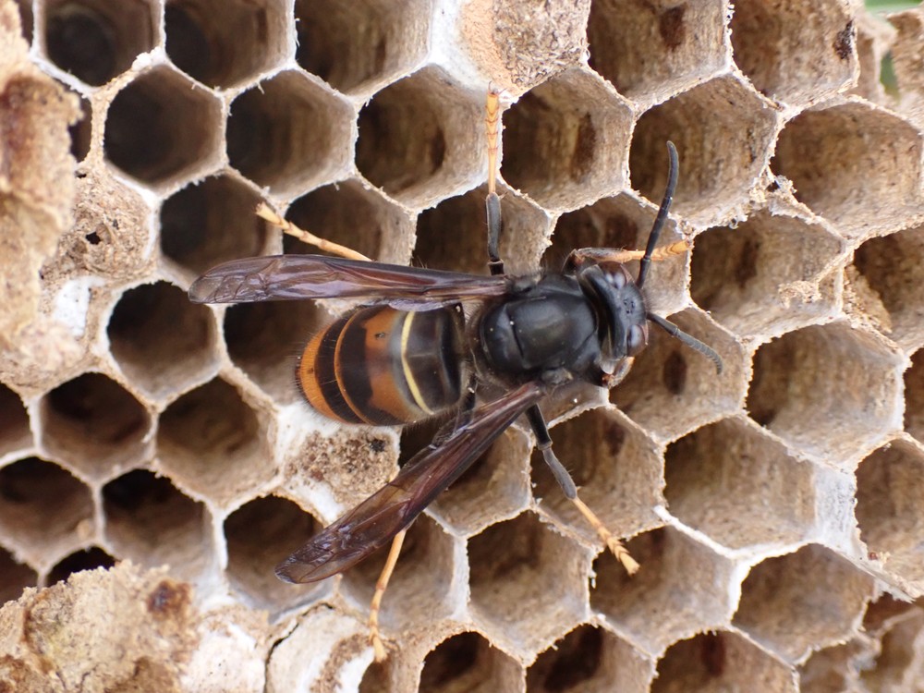
tools/image-viewer/images/VespaVelutina/142253273.jpg
