aggerritsen/VespaSmartTrap-BASE/tools/image-viewer/images/VespaVelutina/142307562.jpg

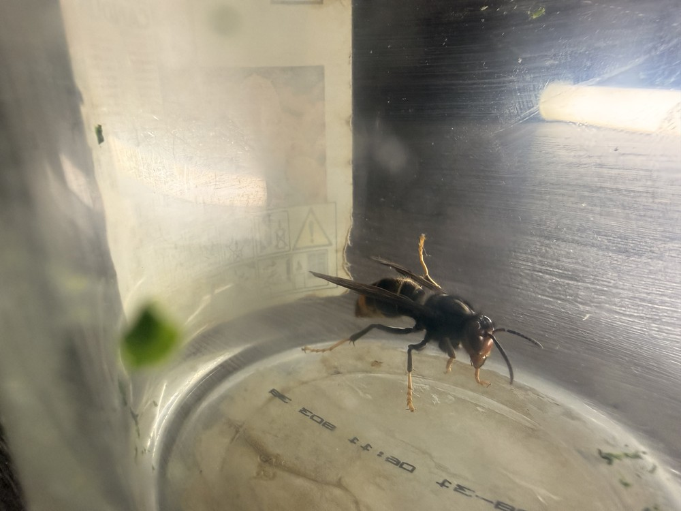
tools/image-viewer/images/VespaVelutina/142307562.jpg
