aggerritsen/VespaSmartTrap-BASE/tools/image-viewer/images/VespaVelutina/142315665.jpg

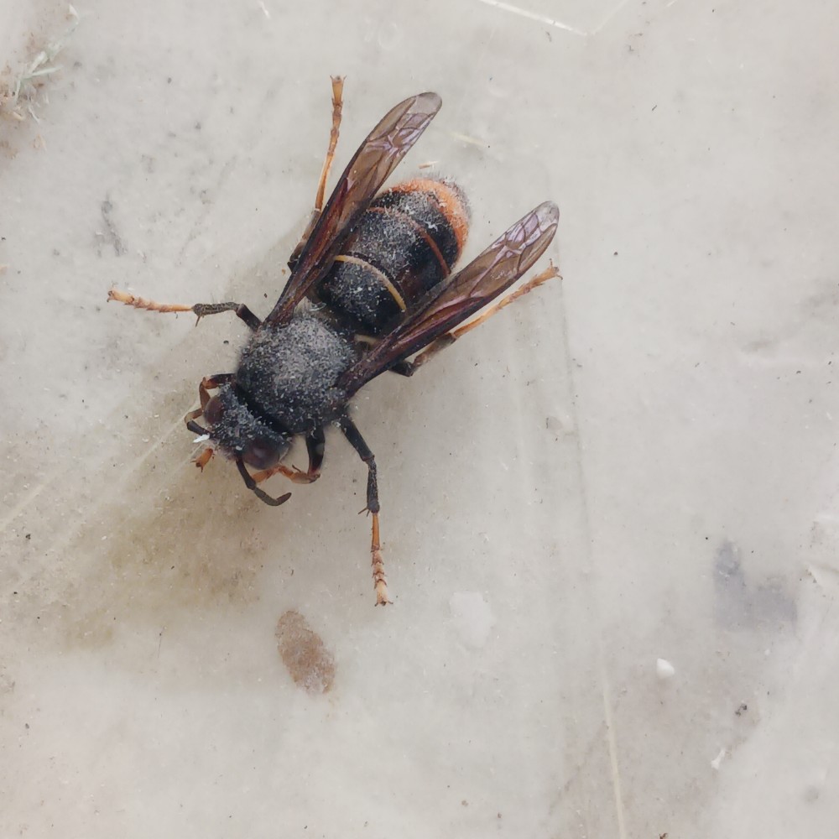
tools/image-viewer/images/VespaVelutina/142315665.jpg
