aggerritsen/VespaSmartTrap-BASE/tools/image-viewer/images/VespaVelutina/142321757.jpg

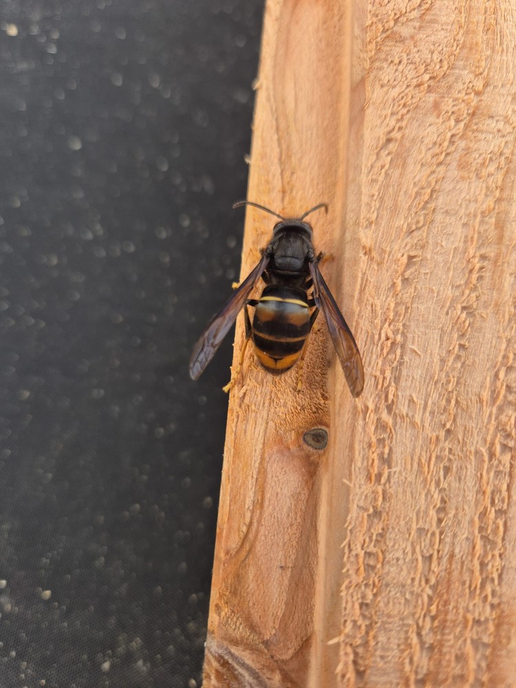
tools/image-viewer/images/VespaVelutina/142321757.jpg
