aggerritsen/VespaSmartTrap-BASE/tools/image-viewer/images/VespaVelutina/142335904.jpg

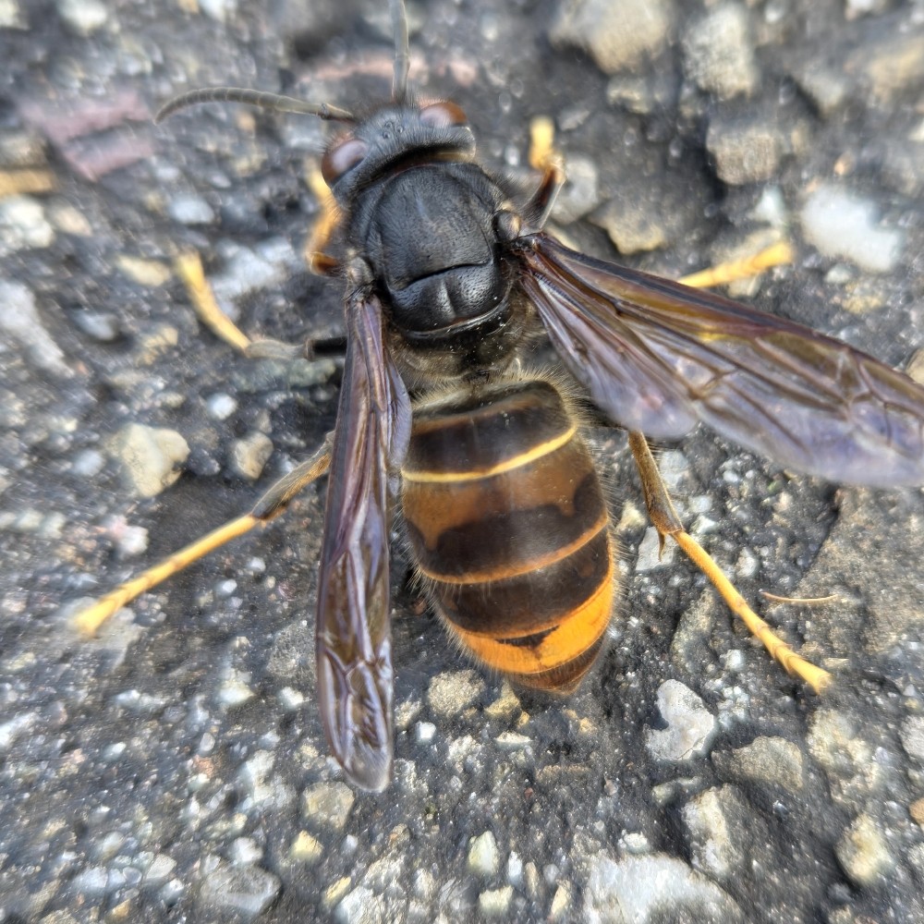
tools/image-viewer/images/VespaVelutina/142335904.jpg
