aggerritsen/VespaSmartTrap-BASE/tools/image-viewer/images/VespaVelutina/142374670.jpg

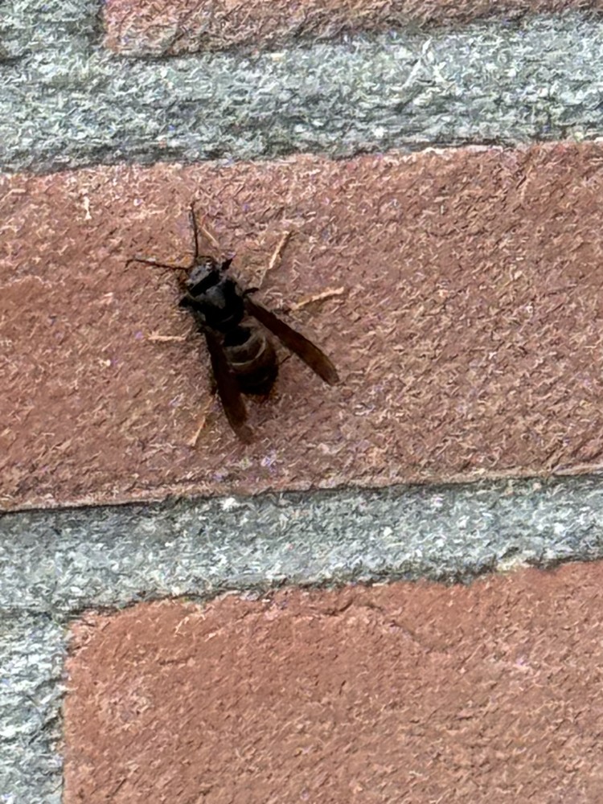
tools/image-viewer/images/VespaVelutina/142374670.jpg
