aggerritsen/VespaSmartTrap-BASE/tools/image-viewer/images/VespaVelutina/142377975.jpg

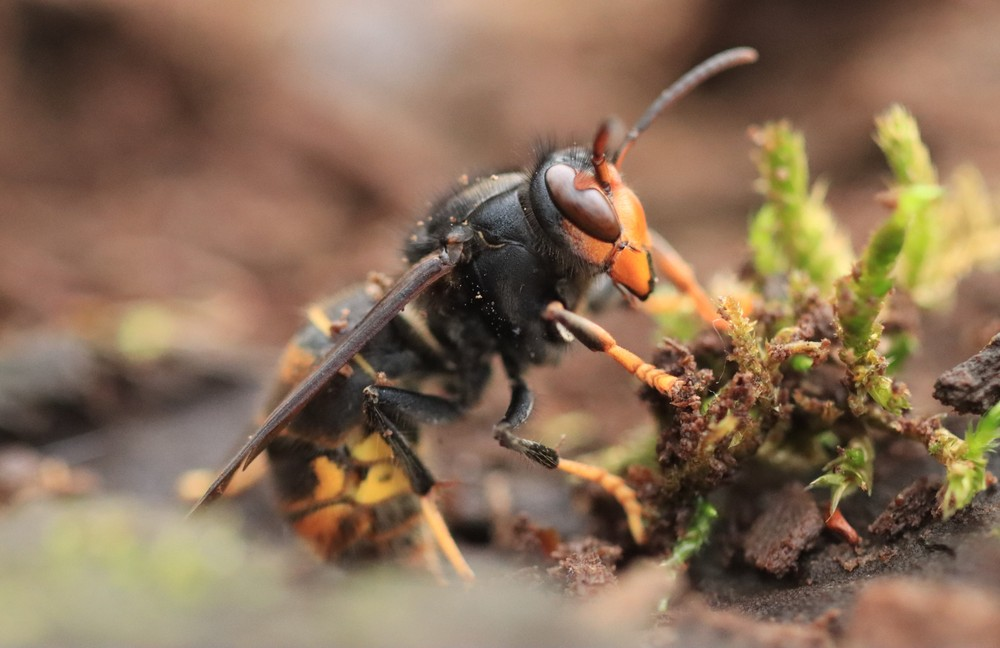
tools/image-viewer/images/VespaVelutina/142377975.jpg
