aggerritsen/VespaSmartTrap-BASE/tools/image-viewer/images/VespaVelutina/142377979.jpg

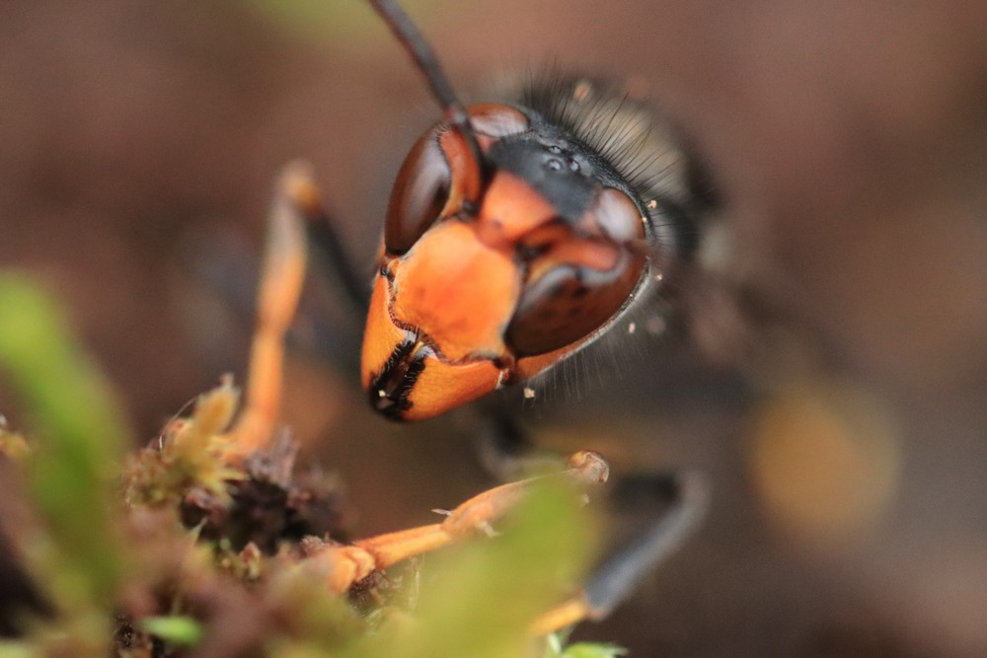
tools/image-viewer/images/VespaVelutina/142377979.jpg
