aggerritsen/VespaSmartTrap-BASE/tools/image-viewer/images/VespaVelutina/142393123.jpg

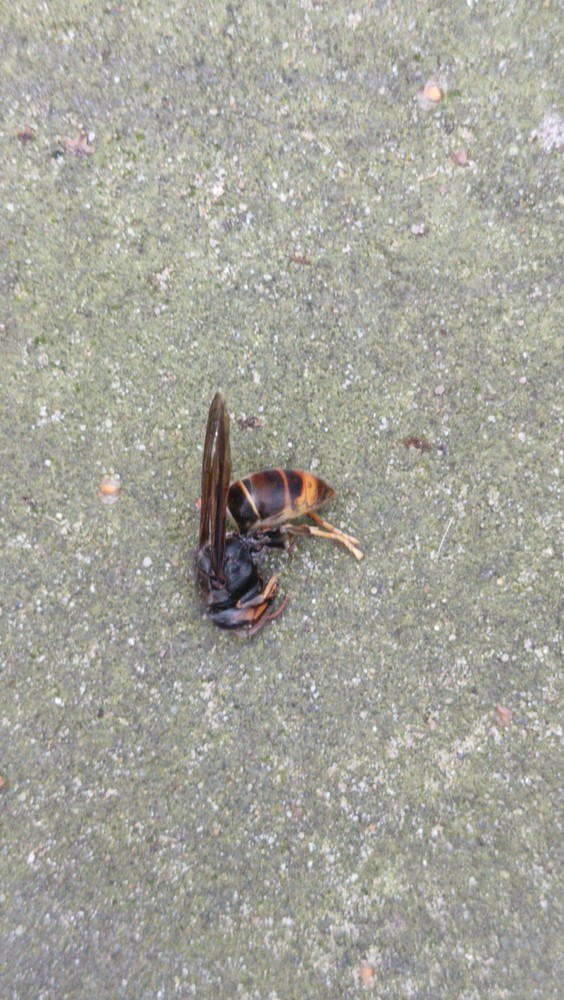
tools/image-viewer/images/VespaVelutina/142393123.jpg
