aggerritsen/VespaSmartTrap-BASE/tools/image-viewer/images/VespaVelutina/142395803.jpg

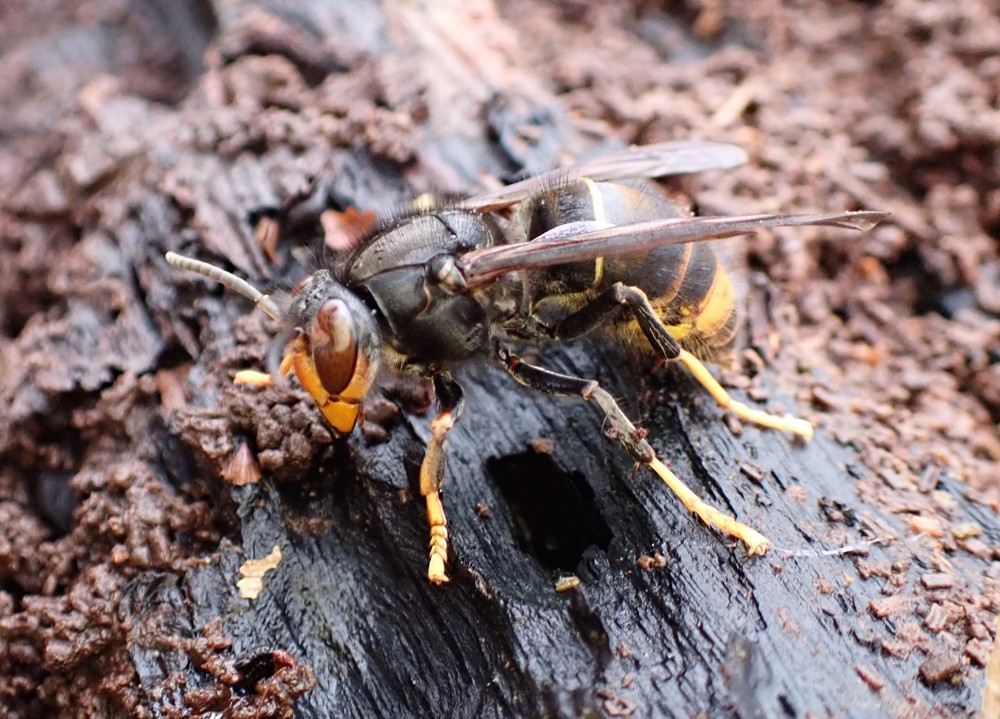
tools/image-viewer/images/VespaVelutina/142395803.jpg
