aggerritsen/VespaSmartTrap-BASE/tools/image-viewer/images/VespaVelutina/142414048.jpg

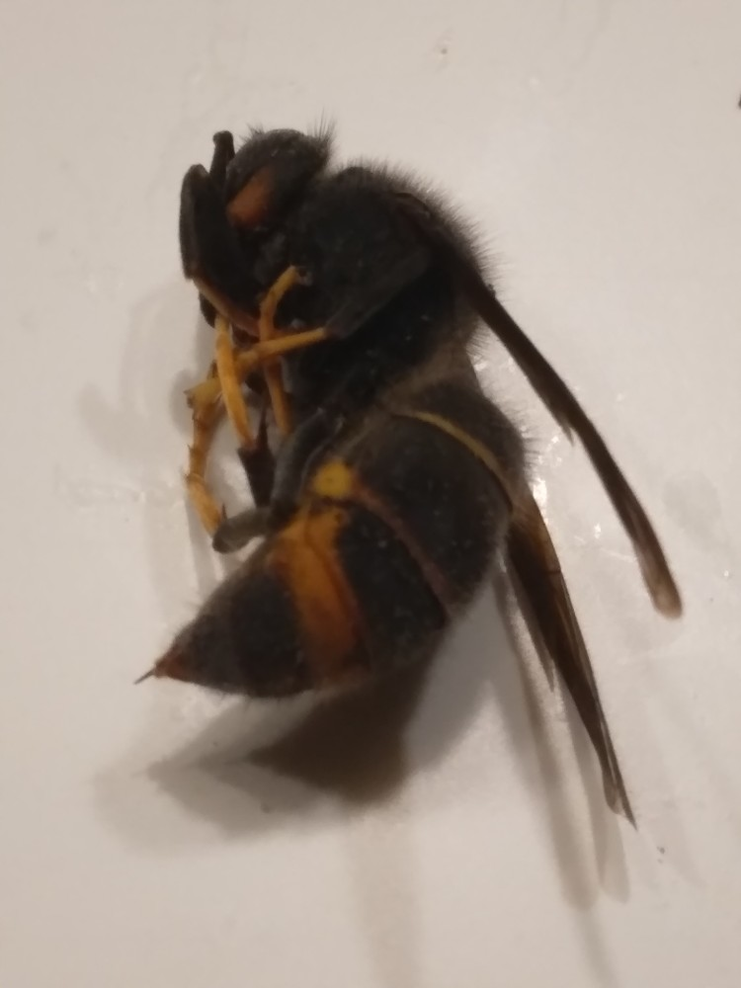
tools/image-viewer/images/VespaVelutina/142414048.jpg
