aggerritsen/VespaSmartTrap-BASE/tools/image-viewer/images/VespaVelutina/142638802.jpg

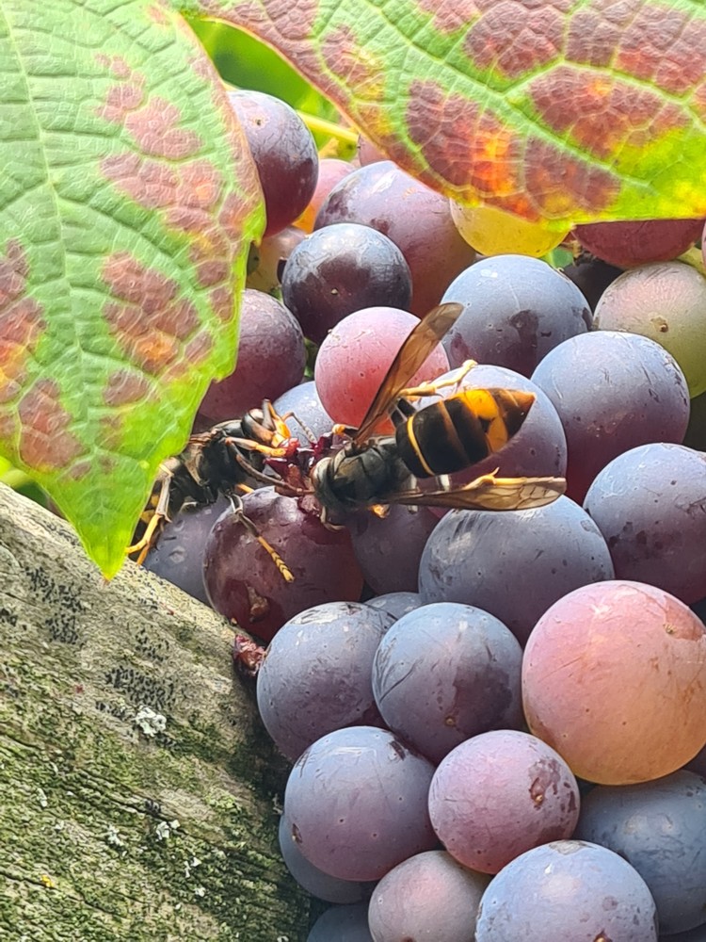
tools/image-viewer/images/VespaVelutina/142638802.jpg
