aggerritsen/VespaSmartTrap-BASE/tools/image-viewer/images/VespaVelutina/142687422.jpg

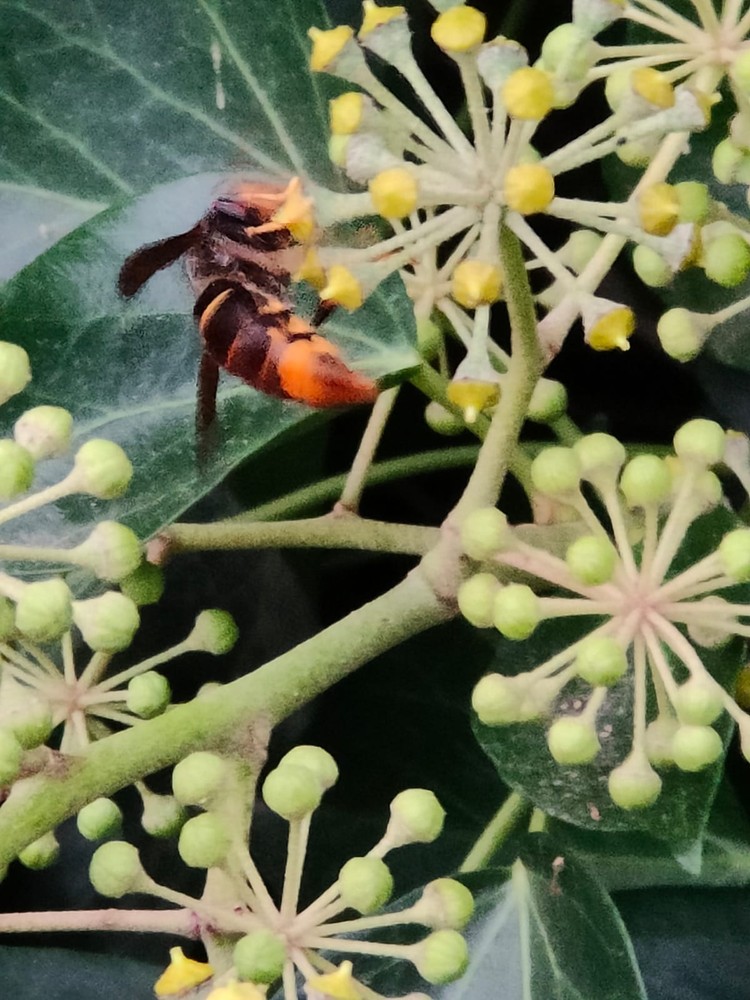
tools/image-viewer/images/VespaVelutina/142687422.jpg
