aggerritsen/VespaSmartTrap-BASE/tools/image-viewer/images/VespaVelutina/142757117.jpg

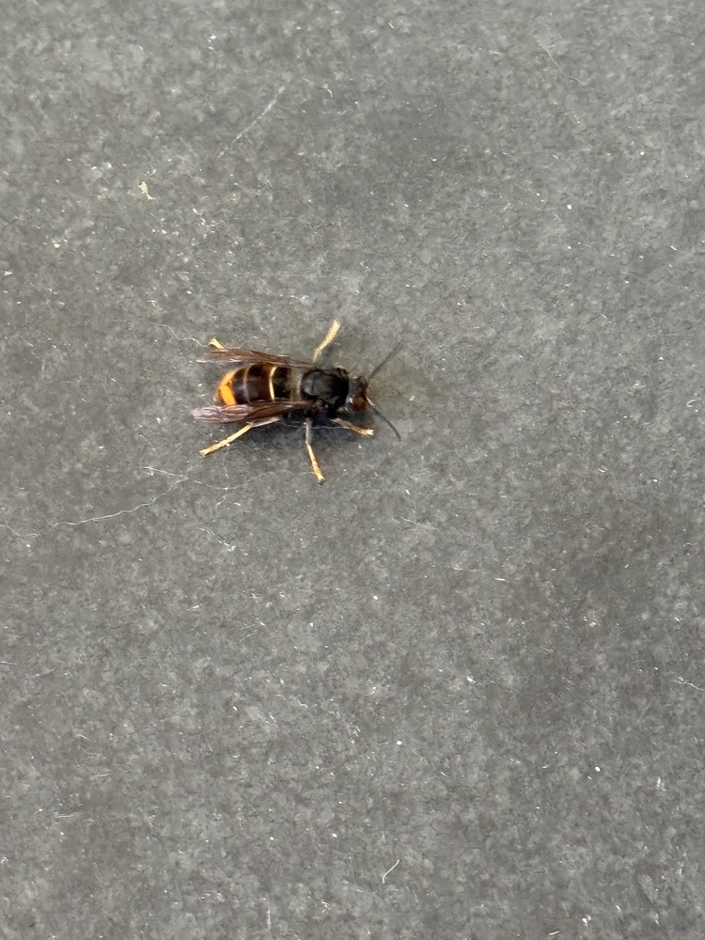
tools/image-viewer/images/VespaVelutina/142757117.jpg
