aggerritsen/VespaSmartTrap-BASE/t-sim/firmware/src/main.cpp

#include <Arduino.h>
#include <string.h>
#include <sys/time.h>
#include <time.h>

#include "esp_sleep.h"
#include "esp_system.h"

#include "sdcard.h"
#include "modem.h"
#include "power.h"
#include "stepper.h"
#include "uart.h"
#include "version.h"
#include "web.h"

static char g_timestamp[32] = {0};
RTC_DATA_ATTR static uint32_t g_deep_sleep_reboot_marker = 0;
static constexpr uint32_t DEEP_SLEEP_REBOOT_MARKER = 0x44535242UL; // DSRB

struct PostResult {
    bool modem_ready = false;
    bool modem_network = false;
    bool modem_ltem = false;
    bool modem_http = false;
    bool modem_powered_down = false;
    bool azure_upload = false;
    bool modem_time = false;
    bool gnss_time = false;
    bool system_time = false;
    bool gnss_ready = false;
    bool gnss_fix = false;
    bool gv2_uart = false;
    bool sd_card = false;
    bool sd_config = false;
    bool power = false;
};

static PostResult g_post;
static ModemGnssInfo g_gnss;
static BaseConfig g_config;
static uint32_t g_last_log_archive_upload_attempt_ms = 0;

/* =========================================================
   UTIL
   ========================================================= */
static void wait_for_serial(uint32_t timeout_ms)
{
    uint32_t start = millis();
    while (!Serial && (millis() - start < timeout_ms)) {
        delay(10);
    }
}

static const char *reset_reason_name(esp_reset_reason_t reason)
{
    switch (reason) {
        case ESP_RST_POWERON: return "POWERON";
        case ESP_RST_EXT: return "EXTERNAL";
        case ESP_RST_SW: return "SOFTWARE";
        case ESP_RST_PANIC: return "PANIC";
        case ESP_RST_INT_WDT: return "INT_WDT";
        case ESP_RST_TASK_WDT: return "TASK_WDT";
        case ESP_RST_WDT: return "WDT";
        case ESP_RST_DEEPSLEEP: return "DEEPSLEEP";
        case ESP_RST_BROWNOUT: return "BROWNOUT";
        case ESP_RST_SDIO: return "SDIO";
        default: return "UNKNOWN";
    }
}

static void print_post_line(const char *name, bool pass, const char *detail = nullptr)
{
    Serial.printf("POST: %-18s [%s]", name, pass ? "PASS" : "FAIL");
    if (detail && detail[0] != '\0')
        Serial.printf(" %s", detail);
    Serial.println();
}

static void print_post_warn(const char *name, const char *detail)
{
    Serial.printf("POST: %-18s [WARN]", name);
    if (detail && detail[0] != '\0')
        Serial.printf(" %s", detail);
    Serial.println();
}

static String current_time_text()
{
    if (!g_post.system_time)
        return "unavailable";

    time_t now = time(nullptr);
    struct tm tm{};
    localtime_r(&now, &tm);

    char buf[32];
    strftime(buf, sizeof(buf), "%Y-%m-%d %H:%M:%S", &tm);
    return String(buf);
}

static bool format_current_time(char *buf, size_t len, const char *format)
{
    if (!buf || len == 0)
        return false;

    buf[0] = '\0';
    if (!g_post.system_time)
        return false;

    time_t now = time(nullptr);
    if (now <= 1700000000)
        return false;

    struct tm tm{};
    if (!localtime_r(&now, &tm))
        return false;

    return strftime(buf, len, format, &tm) > 0;
}

static String current_timestamp_iso()
{
    char buf[32];
    if (format_current_time(buf, sizeof(buf), "%Y-%m-%dT%H:%M:%S"))
        return String(buf);

    return String();
}

static void sanitize_blob_segment(const char *in, char *out, size_t out_len)
{
    if (!out || out_len == 0)
        return;

    out[0] = '\0';
    if (!in)
        return;

    size_t used = 0;
    for (const char *p = in; *p && used + 1 < out_len; p++) {
        char c = *p;
        if ((c >= 'A' && c <= 'Z') ||
            (c >= 'a' && c <= 'z') ||
            (c >= '0' && c <= '9') ||
            c == '-' || c == '_') {
            out[used++] = c;
        } else {
            out[used++] = '_';
        }
    }
    out[used] = '\0';
}

static String current_timestamp_for_filename()
{
    char buf[32];
    if (format_current_time(buf, sizeof(buf), "%Y%m%d_%H%M%S"))
        return String(buf);

    snprintf(buf, sizeof(buf), "uptime_%lu", (unsigned long)millis());
    return String(buf);
}

static bool run_log_upload_post_test()
{
    if (!g_config.azure.log_post_test_enabled) {
        print_post_warn("log_upload_test", "disabled by config");
        return false;
    }
    if (!g_config.logging.upload_enabled) {
        print_post_warn("log_upload_test", "skipped; logging upload disabled");
        return false;
    }
    if (g_config.modem.mode != 2 || !g_post.modem_ltem) {
        print_post_warn("log_upload_test", "skipped; LTE-M unavailable");
        return false;
    }

    String timestamp = current_timestamp_for_filename();
    String local_path = "/log_upload_post_test.jsonl";
    String body;
    body.reserve(220);
    body += "{\"type\":\"log_upload_post_test\",\"timestamp\":\"";
    body += current_timestamp_iso().length() ? current_timestamp_iso() : timestamp;
    body += "\",\"device_name\":\"";
    body += g_config.device_name;
    body += "\",\"result\":\"probe\"}\n";

    if (!sdcard_write_log(local_path.c_str(), body)) {
        print_post_line("log_upload_test", false, "test file write failed");
        return false;
    }

    char device[40] = {0};
    sanitize_blob_segment(g_config.device_name, device, sizeof(device));
    if (!device[0])
        strlcpy(device, "vst-base", sizeof(device));

    const char *prefix = g_config.azure.logs_prefix;
    while (prefix && *prefix == '/')
        prefix++;
    if (!prefix || !prefix[0])
        prefix = "logs";

    char blob_name[160];
    snprintf(blob_name,
             sizeof(blob_name),
             "%s/%s/log_upload_post_test_%s.jsonl",
             prefix,
             device,
             timestamp.c_str());

    bool ok = modem_upload_azure_blob_from_sd(local_path.c_str(),
                                              blob_name,
                                              g_config.modem.apn,
                                              (uint32_t)g_config.azure.runtime_connect_timeout_seconds * 1000UL,
                                              "application/x-ndjson");
    print_post_line("log_upload_test", ok, ok ? blob_name : "upload failed");
    return ok;
}

static const char *path_basename(const char *path)
{
    if (!path)
        return "";
    const char *last = strrchr(path, '/');
    return last ? last + 1 : path;
}

static bool archive_day_from_path(const char *path, char *out, size_t out_len)
{
    if (!path || !out || out_len == 0)
        return false;

    out[0] = '\0';
    const char *marker = strstr(path, "/log/archive/");
    if (!marker)
        return false;

    marker += strlen("/log/archive/");
    if (strlen(marker) < 8 || marker[8] != '/')
        return false;

    for (uint8_t i = 0; i < 8; i++) {
        if (marker[i] < '0' || marker[i] > '9')
            return false;
    }

    if (out_len < 9)
        return false;

    memcpy(out, marker, 8);
    out[8] = '\0';
    return true;
}

static void normalized_blob_prefix(const char *in, char *out, size_t out_len)
{
    if (!out || out_len == 0)
        return;

    out[0] = '\0';
    const char *p = in;
    while (p && *p == '/')
        p++;
    if (!p || !p[0])
        p = "logs";

    strlcpy(out, p, out_len);
    while (out[0]) {
        size_t len = strlen(out);
        if (len == 0 || out[len - 1] != '/')
            break;
        out[len - 1] = '\0';
    }
    if (!out[0])
        strlcpy(out, "logs", out_len);
}

static bool build_log_archive_blob_name(const char *local_path, char *out, size_t out_len)
{
    if (!local_path || !out || out_len == 0)
        return false;

    char prefix[56] = {0};
    char device[40] = {0};
    char day[9] = {0};
    normalized_blob_prefix(g_config.azure.logs_prefix, prefix, sizeof(prefix));
    sanitize_blob_segment(g_config.device_name, device, sizeof(device));
    if (!device[0])
        strlcpy(device, "vst-base", sizeof(device));
    if (!archive_day_from_path(local_path, day, sizeof(day)))
        return false;

    snprintf(out,
             out_len,
             "%s/%s/%s/%s",
             prefix,
             device,
             day,
             path_basename(local_path));
    return out[0] != '\0';
}

static bool log_archive_upload_power_allowed()
{
    PowerSnapshot snapshot;
    if (!power_read_snapshot(snapshot)) {
        Serial.println("LOG_UPLOAD: skipped reason=power_snapshot_unavailable");
        return false;
    }

    if (snapshot.mains_power_present)
        return true;

    uint8_t threshold = g_config.logging.upload_min_battery_percent;
    if (snapshot.battery_present &&
        snapshot.battery_percent >= 0 &&
        snapshot.battery_percent < threshold) {
        Serial.printf("LOG_UPLOAD: skipped reason=battery_low battery=%d min=%u mains_power=NO\n",
                      snapshot.battery_percent,
                      threshold);
        return false;
    }

    return true;
}

static int8_t upload_next_rotated_log_archive(const char *name_prefix, uint8_t &uploaded)
{
    char local_path[128] = {0};
    if (!sdcard_find_next_log_archive_by_prefix(name_prefix, local_path, sizeof(local_path)))
        return 0;

    char blob_name[176] = {0};
    if (!build_log_archive_blob_name(local_path, blob_name, sizeof(blob_name))) {
        Serial.printf("LOG_UPLOAD: skipped reason=bad_archive_path file=%s prefix=%s\n",
                      local_path,
                      name_prefix ? name_prefix : "*");
        return -1;
    }

    Serial.printf("LOG_UPLOAD: begin file=%s blob=%s prefix=%s\n",
                  local_path,
                  blob_name,
                  name_prefix ? name_prefix : "*");
    bool ok = modem_upload_azure_blob_from_sd_runtime(local_path,
                                                      blob_name,
                                                      g_config.modem.apn,
                                                      g_config.modem.operator_auto_select,
                                                      true,
                                                      (uint32_t)g_config.azure.runtime_connect_timeout_seconds * 1000UL,
                                                      true,
                                                      (uint32_t)g_config.azure.runtime_connect_timeout_seconds * 1000UL,
                                                      "application/x-ndjson");
    if (!ok) {
        Serial.printf("LOG_UPLOAD: FAIL file=%s retry=later\n", local_path);
        return -1;
    }

    bool removed = sdcard_remove_file(local_path);
    Serial.printf("LOG_UPLOAD: PASS blob=%s local_delete=%s\n",
                  blob_name,
                  removed ? "OK" : "FAILED");
    uploaded++;
    return 1;
}

static void maybe_upload_rotated_logs()
{
    if (!g_config.logging.upload_enabled)
        return;
    if (!g_post.system_time)
        return;
    if (!sdcard_available())
        return;
    if (g_config.modem.mode != 2 || !g_post.modem_ltem)
        return;

    uint32_t now_ms = millis();
    uint32_t interval_ms = (uint32_t)g_config.logging.upload_interval_minutes * 60000UL;
    if (interval_ms == 0)
        interval_ms = (uint32_t)g_config.logging.rotation_interval_minutes * 60000UL;
    if (interval_ms == 0)
        interval_ms = 3600000UL;

    if (g_last_log_archive_upload_attempt_ms == 0) {
        if (now_ms < 60000UL)
            return;
    } else if ((uint32_t)(now_ms - g_last_log_archive_upload_attempt_ms) < interval_ms) {
        return;
    }
    g_last_log_archive_upload_attempt_ms = now_ms;

    if (!log_archive_upload_power_allowed())
        return;

    uint8_t max_files = g_config.logging.upload_max_files_per_run;
    if (max_files == 0)
        max_files = 1;

    uint8_t uploaded = 0;
    bool stop_uploads = false;
    const char *fair_prefixes[] = {"frames", "health", "power"};
    for (size_t i = 0; i < sizeof(fair_prefixes) / sizeof(fair_prefixes[0]) && uploaded < max_files; i++) {
        int8_t result = upload_next_rotated_log_archive(fair_prefixes[i], uploaded);
        if (result < 0) {
            stop_uploads = true;
            break;
        }
    }

    while (!stop_uploads && uploaded < max_files) {
        int8_t result = upload_next_rotated_log_archive(nullptr, uploaded);
        if (result <= 0) {
            if (uploaded == 0)
                Serial.println("LOG_UPLOAD: no archive files pending");
            break;
        }
    }

    Serial.printf("LOG_UPLOAD: done uploaded=%u max=%u\n", uploaded, max_files);
}

static String post_sms_probe_message()
{
    String s;
    s.reserve(120);
    s += "VST SMS test from ";
    s += g_config.device_name;
    s += ". Time: ";
    String timestamp = current_timestamp_iso();
    s += timestamp.length() ? timestamp : "unavailable";
    s += ". APN: ";
    s += g_config.modem.apn[0] ? g_config.modem.apn : "-";
    return s;
}

static bool send_post_sms_probe()
{
    if (!g_config.sms.enabled) {
        print_post_warn("sms_probe", "skipped by config");
        return false;
    }
    if (!g_config.sms.post_test_enabled) {
        print_post_warn("sms_probe", "post test disabled");
        return false;
    }
    if (g_config.sms.recipient_count == 0) {
        print_post_warn("sms_probe", "no recipients");
        return false;
    }
    if (!g_config.modem.direct_sms) {
        print_post_warn("sms_probe", "skipped; selected provider direct_sms=NO");
        return false;
    }
    if (!g_post.modem_ready || !g_post.modem_network) {
        print_post_warn("sms_probe", "skipped; modem network unavailable");
        return false;
    }

    String message = post_sms_probe_message();
    bool all_ok = true;
    for (uint8_t i = 0; i < g_config.sms.recipient_count; i++) {
        const SmsConfig::Recipient &recipient = g_config.sms.recipients[i];
        if (!recipient.number[0])
            continue;

        Serial.printf("POST: SMS probe begin recipient=%s number=%s\n",
                      recipient.name[0] ? recipient.name : "-",
                      recipient.number);
        bool ok = modem_send_sms_text(recipient.number, message.c_str());
        Serial.printf("POST: SMS probe %s recipient=%s number=%s\n",
                      ok ? "PASS" : "FAIL",
                      recipient.name[0] ? recipient.name : "-",
                      recipient.number);
        all_ok = all_ok && ok;
        if (!ok)
            break;
    }

    print_post_line("sms_probe", all_ok);
    return all_ok;
}

static String current_timestamp_compact()
{
    char buf[32];
    if (format_current_time(buf, sizeof(buf), "%Y%m%d_%H%M%S"))
        return String(buf);

    return String();
}

static bool current_local_time(struct tm &tm)
{
    time_t now = time(nullptr);
    if (now <= 1700000000)
        return false;

    return localtime_r(&now, &tm) != nullptr;
}

static bool is_hour_in_sleep_window(uint8_t hour, const PowerConfig &config)
{
    uint8_t start = config.deep_sleep_start_hour;
    uint8_t end = config.deep_sleep_end_hour;

    if (start < end)
        return hour >= start && hour < end;

    return hour >= start || hour < end;
}

static uint32_t seconds_until_sleep_window_end(const struct tm &tm, const PowerConfig &config)
{
    int now_seconds = tm.tm_hour * 3600 + tm.tm_min * 60 + tm.tm_sec;
    int end_seconds = config.deep_sleep_end_hour * 3600;
    int delta = end_seconds - now_seconds;

    if (delta <= 0)
        delta += 24 * 3600;

    return (uint32_t)delta;
}

static const char *deep_sleep_reason()
{
    switch (g_config.power.deep_sleep) {
        case 1: return "scheduled_night_window";
        case 2: return "scheduled_battery_only";
        default: return "disabled";
    }
}

static bool deep_sleep_power_condition_allows(const char *phase)
{
    if (g_config.power.deep_sleep != 2)
        return true;

    static uint32_t last_loop_check_ms = 0;
    if (phase && strcmp(phase, "loop") == 0) {
        uint32_t now_ms = millis();
        uint32_t interval_ms = g_config.power.log_interval_seconds * 1000UL;
        if (interval_ms == 0)
            interval_ms = 60000UL;
        if (last_loop_check_ms != 0 && now_ms - last_loop_check_ms < interval_ms)
            return false;
        last_loop_check_ms = now_ms;
    }

    PowerSnapshot snapshot;
    if (!power_read_snapshot(snapshot)) {
        Serial.printf("POWER: sleep schedule skipped phase=%s reason=power_snapshot_unavailable mode=2\n", phase);
        return false;
    }

    bool battery_only_discharge = snapshot.battery_present && snapshot.discharging && !snapshot.mains_power_present;

    if (!battery_only_discharge) {
        Serial.printf("POWER: sleep schedule skipped phase=%s reason=mains_power_or_not_discharging mode=2 battery_present=%s discharging=%s mains_power=%s vbus_good=%s vbus_in=%s vbus_mv=%u solar=%s\n",
                      phase,
                      snapshot.battery_present ? "YES" : "NO",
                      snapshot.discharging ? "YES" : "NO",
                      snapshot.mains_power_present ? "YES" : "NO",
                      snapshot.vbus_good ? "YES" : "NO",
                      snapshot.vbus_in ? "YES" : "NO",
                      (unsigned)snapshot.vbus_mv,
                      snapshot.solar_suspect ? "SUSPECT" : "NO");
        return false;
    }

    Serial.printf("POWER: sleep mode 2 allowed phase=%s battery_present=%s discharging=%s mains_power=%s vbus_good=%s vbus_in=%s vbus_mv=%u solar=%s\n",
                  phase,
                  snapshot.battery_present ? "YES" : "NO",
                  snapshot.discharging ? "YES" : "NO",
                  snapshot.mains_power_present ? "YES" : "NO",
                  snapshot.vbus_good ? "YES" : "NO",
                  snapshot.vbus_in ? "YES" : "NO",
                  (unsigned)snapshot.vbus_mv,
                  snapshot.solar_suspect ? "SUSPECT" : "NO");
    return true;
}

static void enter_deep_sleep_until(uint32_t sleep_seconds, const char *reason = nullptr)
{
    if (sleep_seconds < 60)
        sleep_seconds = 60;

    if (!reason || !reason[0])
        reason = deep_sleep_reason();
    Serial.printf("POWER: entering deep sleep for %lu seconds reason=%s\n",
                  (unsigned long)sleep_seconds,
                  reason);
    sdcard_append_log("/power.log", String("{\"event\":\"deep_sleep_enter\",\"device_name\":\"") +
                                      String(g_config.device_name) +
                                      String("\",\"seconds\":") +
                                      String((unsigned long)sleep_seconds) +
                                      String(",\"reason\":\"") +
                                      String(reason) +
                                      String("\"}\n"));
    gv2_prepare_for_sleep(g_config.uart);
    modem_prepare_for_sleep();
    g_deep_sleep_reboot_marker = DEEP_SLEEP_REBOOT_MARKER;
    Serial.flush();
    esp_sleep_enable_timer_wakeup((uint64_t)sleep_seconds * 1000000ULL);
    esp_deep_sleep_start();
}

static uint32_t low_battery_sleep_seconds(uint16_t wake_interval_minutes, const char **schedule_note)
{
    uint32_t base_seconds = (uint32_t)wake_interval_minutes * 60UL;
    if (schedule_note)
        *schedule_note = "hourly_check";

    if (!g_config.power.deep_sleep)
        return base_seconds;

    struct tm now_tm{};
    if (!current_local_time(now_tm))
        return base_seconds;

    if (is_hour_in_sleep_window((uint8_t)now_tm.tm_hour, g_config.power)) {
        if (schedule_note)
            *schedule_note = "inside_sleep_window";
        return seconds_until_sleep_window_end(now_tm, g_config.power);
    }

    time_t now = time(nullptr);
    time_t wake_time = now + base_seconds;
    struct tm wake_tm{};
    if (wake_time > 1700000000 &&
        localtime_r(&wake_time, &wake_tm) &&
        is_hour_in_sleep_window((uint8_t)wake_tm.tm_hour, g_config.power)) {
        if (schedule_note)
            *schedule_note = "extended_to_sleep_window_end";
        return base_seconds + seconds_until_sleep_window_end(wake_tm, g_config.power);
    }

    return base_seconds;
}

static bool sleep_if_battery_too_low(const char *phase)
{
    uint8_t threshold = g_config.power.low_battery_sleep_percent;
    if (threshold == 0)
        return false;

    static uint32_t last_loop_check_ms = 0;
    if (phase && strcmp(phase, "loop") == 0) {
        uint32_t now_ms = millis();
        uint32_t interval_ms = g_config.power.log_interval_seconds * 1000UL;
        if (interval_ms == 0 || interval_ms > 60000UL)
            interval_ms = 60000UL;
        if (last_loop_check_ms != 0 && now_ms - last_loop_check_ms < interval_ms)
            return false;
        last_loop_check_ms = now_ms;
    }

    PowerSnapshot snapshot;
    if (!power_read_snapshot(snapshot)) {
        Serial.printf("POWER: low-battery sleep skipped phase=%s reason=power_snapshot_unavailable\n", phase);
        return false;
    }

    bool low_battery = snapshot.battery_present &&
                       !snapshot.mains_power_present &&
                       snapshot.battery_percent >= 0 &&
                       snapshot.battery_percent <= threshold;
    const char *action = low_battery ? "sleep" : "continue";
    bool loop_phase = phase && strcmp(phase, "loop") == 0;
    if (!loop_phase || low_battery) {
        Serial.printf("POWER: low-battery check phase=%s battery_present=%s battery=%d%% battery_mv=%u threshold=%u%% mains_power=%s vbus_mv=%u solar=%s action=%s\n",
                      phase,
                      snapshot.battery_present ? "YES" : "NO",
                      snapshot.battery_percent,
                      (unsigned)snapshot.battery_mv,
                      threshold,
                      snapshot.mains_power_present ? "YES" : "NO",
                      (unsigned)snapshot.vbus_mv,
                      snapshot.solar_suspect ? "SUSPECT" : "NO",
                      action);
    }
    if (!low_battery)
        return false;

    const char *schedule_note = nullptr;
    uint32_t sleep_seconds = low_battery_sleep_seconds(g_config.power.low_battery_wake_interval_minutes,
                                                       &schedule_note);
    uint32_t actual_wake_minutes = sleep_seconds / 60UL;
    Serial.printf("POWER: low-battery sleep phase=%s battery=%d%% threshold=%u%% configured_wake_minutes=%u actual_wake_minutes=%lu schedule=%s mains_power=%s vbus_mv=%u solar=%s\n",
                  phase,
                  snapshot.battery_percent,
                  threshold,
                  g_config.power.low_battery_wake_interval_minutes,
                  (unsigned long)actual_wake_minutes,
                  schedule_note ? schedule_note : "-",
                  snapshot.mains_power_present ? "YES" : "NO",
                  (unsigned)snapshot.vbus_mv,
                  snapshot.solar_suspect ? "SUSPECT" : "NO");
    sdcard_append_log("/power.log", String("{\"event\":\"low_battery_sleep\",\"device_name\":\"") +
                                      String(g_config.device_name) +
                                      String("\",\"phase\":\"") +
                                      String(phase ? phase : "") +
                                      String("\",\"battery_percent\":") +
                                      String(snapshot.battery_percent) +
                                      String(",\"threshold_percent\":") +
                                      String(threshold) +
                                      String(",\"configured_wake_minutes\":") +
                                      String(g_config.power.low_battery_wake_interval_minutes) +
                                      String(",\"actual_wake_minutes\":") +
                                      String((unsigned long)actual_wake_minutes) +
                                      String(",\"schedule\":\"") +
                                      String(schedule_note ? schedule_note : "") +
                                      String("\"") +
                                      String("}\n"));
    enter_deep_sleep_until(sleep_seconds, "low_battery_protection");
    return true;
}

static void sleep_if_in_configured_window(const char *phase)
{
    if (!g_config.power.deep_sleep)
        return;

    struct tm tm{};
    if (!current_local_time(tm)) {
        static uint32_t last_loop_no_time_log_ms = 0;
        if (phase && strcmp(phase, "loop") == 0) {
            uint32_t now_ms = millis();
            uint32_t interval_ms = g_config.power.log_interval_seconds * 1000UL;
            if (interval_ms == 0)
                interval_ms = 60000UL;
            if (last_loop_no_time_log_ms != 0 && now_ms - last_loop_no_time_log_ms < interval_ms)
                return;
            last_loop_no_time_log_ms = now_ms;
        }
        Serial.printf("POWER: sleep schedule skipped phase=%s reason=no_valid_system_time\n", phase);
        return;
    }

    if (!is_hour_in_sleep_window((uint8_t)tm.tm_hour, g_config.power))
        return;

    if (!deep_sleep_power_condition_allows(phase))
        return;

    uint32_t sleep_seconds = seconds_until_sleep_window_end(tm, g_config.power);
    Serial.printf("POWER: sleep window active phase=%s mode=%u now=%02d:%02d:%02d window=%02u:00-%02u:00\n",
                  phase,
                  g_config.power.deep_sleep,
                  tm.tm_hour,
                  tm.tm_min,
                  tm.tm_sec,
                  g_config.power.deep_sleep_start_hour,
                  g_config.power.deep_sleep_end_hour);
    enter_deep_sleep_until(sleep_seconds);
}

static String make_post_summary_text()
{
    String s;
    s.reserve(900);

    s += "==================================================\n";
    s += "POST SUMMARY\n";
    s += "==================================================\n";
    s += "firmware=receiver build=2026-05-04 post-log-v2\n";
    s += "software_name=";
    s += VST_BASE_SOFTWARE_NAME;
    s += "\n";
    s += "software_version=";
    s += VST_BASE_SOFTWARE_VERSION;
    s += "\n";
    s += "device_name=";
    s += g_config.device_name;
    s += "\n";
    s += "post_log=";
    s += g_config.logging.post_log;
    s += "\n";
    s += "image_prefix=";
    s += g_config.logging.image_prefix;
    s += "\n";
    s += "log_rotation_interval_minutes=";
    s += g_config.logging.rotation_interval_minutes;
    s += "\n";
    s += "log_retention_days=";
    s += g_config.logging.retention_days;
    s += "\n";
    s += "log_upload=";
    s += g_config.logging.upload_enabled ? "YES" : "NO";
    s += " interval_minutes=";
    s += g_config.logging.upload_interval_minutes;
    s += " max_files_per_run=";
    s += g_config.logging.upload_max_files_per_run;
    s += " min_battery_percent=";
    s += g_config.logging.upload_min_battery_percent;
    s += "\n";
    s += "azure_photos_prefix=";
    s += g_config.azure.photos_prefix;
    s += "\n";
    s += "azure_logs_prefix=";
    s += g_config.azure.logs_prefix;
    s += "\n";
    s += "azure_log_post_test=";
    s += g_config.azure.log_post_test_enabled ? "YES" : "NO";
    s += "\n";
    s += "feature_gnss_probe=";
    s += g_config.features.gnss_probe ? "YES" : "NO";
    s += "\n";
    s += "feature_ack_frames=";
    s += g_config.features.ack_frames ? "YES" : "NO";
    s += "\n";
    s += "log_policy=overwrite_at_boot\n";
    s += "timestamp_compact=";
    s += (g_post.modem_time || g_post.gnss_time) ? g_timestamp : "unavailable";
    s += "\n";
    s += "timestamp_source=";
    s += g_post.modem_time ? "modem_network" : (g_post.gnss_time ? "gnss_utc" : "unavailable");
    s += "\n";
    s += "system_time_local=";
    s += current_time_text();
    s += "\n";
    s += "reset_reason=";
    s += reset_reason_name(esp_reset_reason());
    s += " (";
    s += (int)esp_reset_reason();
    s += ")\n";
    s += "sdk=";
    s += ESP.getSdkVersion();
    s += "\n";
    s += "chip=";
    s += ESP.getChipModel();
    s += " rev=";
    s += ESP.getChipRevision();
    s += " cores=";
    s += ESP.getChipCores();
    s += " cpu_mhz=";
    s += ESP.getCpuFreqMHz();
    s += "\n";
    s += "flash_size=";
    s += ESP.getFlashChipSize();
    s += " sketch_size=";
    s += ESP.getSketchSize();
    s += " free_sketch=";
    s += ESP.getFreeSketchSpace();
    s += "\n";
    s += "heap_free=";
    s += ESP.getFreeHeap();
    s += " heap_min=";
    s += ESP.getMinFreeHeap();
    s += " heap_size=";
    s += ESP.getHeapSize();
    s += "\n";
    s += "psram_found=";
    s += psramFound() ? "YES" : "NO";
    s += " psram_size=";
    s += ESP.getPsramSize();
    s += " psram_free=";
    s += ESP.getFreePsram();
    s += "\n";
    s += "efuse_mac=";
    char mac[16];
    snprintf(mac, sizeof(mac), "%012llX", ESP.getEfuseMac());
    s += mac;
    s += "\n";
    s += "usb_serial=COM5 baud=115200\n";
    s += "gv2_uart=Serial2";
    s += " RX=";
    s += g_config.uart.rx_gpio;
    s += " TX=";
    s += g_config.uart.tx_gpio;
    s += " baud=";
    s += g_config.uart.baud;
    s += " protocol=VSTJ/VSTS/VSTH/VSTE+CRC32";
    s += "\n";
    s += "modem_at=";
    s += g_post.modem_ready ? "PASS" : "FAIL";
    s += "\n";
    s += "modem_mode=";
    s += g_config.modem.mode;
    s += "\n";
    s += "modem_apn=";
    s += g_config.modem.apn;
    s += "\n";
    s += "modem_direct_sms=";
    s += g_config.modem.direct_sms ? "YES" : "NO";
    s += "\n";
    s += "modem_apn_autodetect=";
    s += g_config.modem.apn_autodetect ? "YES" : "NO";
    s += "\n";
    s += "modem_apn_test_all=";
    s += g_config.modem.apn_test_all ? "YES" : "NO";
    s += "\n";
    s += "modem_validate_http_egress=";
    s += g_config.modem.validate_http_egress ? "YES" : "NO";
    s += "\n";
    s += "modem_operator_auto_select=";
    s += g_config.modem.operator_auto_select ? "YES" : "NO";
    s += "\n";
    s += "modem_preferred_radio_mode=";
    s += g_config.modem.preferred_radio_mode;
    s += "\n";
    s += "modem_apn_candidates=";
    s += g_config.modem.apn_candidate_count;
    s += "\n";
    s += "modem_ltem=";
    s += g_post.modem_ltem ? "PASS" : (g_config.modem.mode == 2 ? "FAIL" : "SKIPPED");
    s += "\n";
    s += "modem_http_egress=";
    if (g_config.modem.mode != 2 || !g_config.modem.validate_http_egress)
        s += "SKIPPED";
    else
        s += g_post.modem_http ? "PASS" : "FAIL";
    s += "\n";
    s += "azure_upload=";
    s += g_config.modem.mode == 2 ? "PROBE_DISABLED" : "SKIPPED";
    s += "\n";
    s += "modem_lookup_primary=";
    s += g_config.modem.lookup_primary;
    s += "\n";
    s += "modem_lookup_secondary=";
    s += g_config.modem.lookup_secondary;
    s += "\n";
    s += "modem_timestamp=";
    s += g_post.modem_time ? "PASS " : "FAIL ";
    s += g_post.modem_time ? g_timestamp : "no_valid_network_time";
    s += "\n";
    s += "cellular_time_status=";
    s += g_post.modem_time ? "network_time_valid" : "network_registration_timeout_or_missing_sim";
    s += "\n";
    s += "gnss_timestamp=";
    s += g_post.gnss_time ? "PASS " : "FAIL ";
    s += g_post.gnss_time ? g_timestamp : "unavailable";
    s += "\n";
    s += "gnss_time_status=";
    if (g_post.gnss_time)
        s += "trusted_position_time";
    else if (!g_post.gnss_ready)
        s += "gnss_command_unavailable";
    else if (!g_gnss.position_valid)
        s += "invalid_position_or_missing_gnss_antenna";
    else
        s += "not_used";
    s += "\n";
    s += "system_time=";
    s += g_post.system_time ? "PASS" : "FAIL";
    s += "\n";
    s += "gnss_command=";
    s += g_post.gnss_ready ? "PASS" : "FAIL";
    s += "\n";
    s += "gnss_powered=";
    s += g_gnss.powered ? "YES" : "NO";
    s += "\n";
    s += "gnss_fix=";
    s += g_post.gnss_fix ? "YES" : "NO";
    s += "\n";
    s += "gnss_raw_fix=";
    s += g_gnss.fix ? "YES" : "NO";
    s += "\n";
    s += "gnss_position_valid=";
    s += g_gnss.position_valid ? "YES" : "NO";
    s += "\n";
    s += "gnss_utc=";
    s += g_gnss.utc[0] ? g_gnss.utc : "unavailable";
    s += "\n";
    s += "gnss_latitude=";
    s += g_gnss.latitude[0] ? g_gnss.latitude : "unavailable";
    s += "\n";
    s += "gnss_longitude=";
    s += g_gnss.longitude[0] ? g_gnss.longitude : "unavailable";
    s += "\n";
    s += "gnss_altitude_m=";
    s += g_gnss.altitude_m[0] ? g_gnss.altitude_m : "unavailable";
    s += "\n";
    s += "gnss_speed_kph=";
    s += g_gnss.speed_kph[0] ? g_gnss.speed_kph : "unavailable";
    s += "\n";
    s += "gnss_satellites_view=";
    s += g_gnss.satellites[0] ? g_gnss.satellites : "unavailable";
    s += "\n";
    s += "gnss_satellite_count=";
    s += g_gnss.satellite_count;
    s += "\n";
    s += "gnss_raw=";
    s += g_gnss.raw[0] ? g_gnss.raw : "unavailable";
    s += "\n";
    s += "gv2_uart_status=";
    s += g_post.gv2_uart ? "PASS" : "FAIL";
    s += "\n";
    s += "sd_card=";
    s += g_post.sd_card ? "PASS" : "FAIL";
    s += "\n";
    s += "sd_config=";
    s += g_post.sd_config ? "PASS /config.json" : "FAIL";
    s += "\n";
    s += "stepper_speed_steps_per_second=";
    s += g_config.stepper.speed_steps_per_second;
    s += "\n";
    s += "stepper_rotation_degrees=";
    s += g_config.stepper.rotation_degrees;
    s += "\n";
    s += "stepper_reverse_wait_ms=";
    s += g_config.stepper.reverse_wait_ms;
    s += "\n";
    s += "stepper_steps_per_revolution=";
    s += g_config.stepper.steps_per_revolution;
    s += "\n";
    s += "stepper_start_direction=";
    s += g_config.stepper.start_direction;
    s += "\n";
    s += "inference_confidence_threshold=";
    s += String(g_config.inference.confidence_threshold, 3);
    s += "\n";
    s += "inference_photo_mode=";
    s += g_config.inference.photo_mode;
    s += "\n";
    s += "inference_detected_class=";
    s += g_config.inference.detected_class;
    s += "\n";
    s += "inference_occurrence=";
    s += g_config.inference.occurrence;
    s += "\n";
    s += "inference_occurrence_window_seconds=";
    s += g_config.inference.occurrence_window_seconds;
    s += "\n";
    s += "power_log_interval_seconds=";
    s += g_config.power.log_interval_seconds;
    s += "\n";
    s += "power_solar_auto_optimize=";
    s += g_config.power.solar_auto_optimize ? "YES" : "NO";
    s += "\n";
    s += "health_led=";
    s += g_config.health.led;
    s += "\n";
    s += "power_deep_sleep=";
    s += g_config.power.deep_sleep;
    s += "\n";
    s += "power_deep_sleep_window=";
    if (g_config.power.deep_sleep_start_hour < 10)
        s += "0";
    s += g_config.power.deep_sleep_start_hour;
    s += ":00-";
    if (g_config.power.deep_sleep_end_hour < 10)
        s += "0";
    s += g_config.power.deep_sleep_end_hour;
    s += ":00\n";
    s += "power_low_battery_sleep_percent=";
    s += g_config.power.low_battery_sleep_percent;
    s += "\n";
    s += "power_low_battery_wake_interval_minutes=";
    s += g_config.power.low_battery_wake_interval_minutes;
    s += "\n";
    s += "power_reboot_cron=";
    s += g_config.power.reboot_cron[0] ? g_config.power.reboot_cron : "-";
    s += "\n";
    s += "power_reboot_after_deep_sleep_wakeup=";
    s += g_config.power.reboot_after_deep_sleep_wakeup ? "YES" : "NO";
    s += "\n";
    s += "azure_cooldown_minutes=";
    s += g_config.azure.cooldown_minutes;
    s += "\n";
    s += "azure_failure_cooldown_seconds=";
    s += g_config.azure.failure_cooldown_seconds;
    s += "\n";
    s += "azure_runtime_connect_timeout_seconds=";
    s += g_config.azure.runtime_connect_timeout_seconds;
    s += "\n";
    s += "==================================================\n\n";

    return s;
}

static void print_system_info()
{
    Serial.println();
    Serial.println("==================================================");
    Serial.println(" POWER-ON SELF TEST: T-SIM7080G-S3 RECEIVER");
    Serial.println("==================================================");
    Serial.printf("POST: firmware=receiver version=%s build=2026-05-04 debug-com5\n", VST_BASE_SOFTWARE_VERSION);
    Serial.printf("POST: reset_reason=%s (%d)\n",
                  reset_reason_name(esp_reset_reason()),
                  (int)esp_reset_reason());
    Serial.printf("POST: sdk=%s\n", ESP.getSdkVersion());
    Serial.printf("POST: chip=%s rev=%u cores=%u cpu=%uMHz\n",
                  ESP.getChipModel(),
                  ESP.getChipRevision(),
                  ESP.getChipCores(),
                  ESP.getCpuFreqMHz());
    Serial.printf("POST: flash_size=%u sketch_size=%u free_sketch=%u\n",
                  ESP.getFlashChipSize(),
                  ESP.getSketchSize(),
                  ESP.getFreeSketchSpace());
    Serial.printf("POST: heap_free=%u heap_min=%u heap_size=%u\n",
                  ESP.getFreeHeap(),
                  ESP.getMinFreeHeap(),
                  ESP.getHeapSize());
    Serial.printf("POST: psram_found=%s psram_size=%u psram_free=%u\n",
                  psramFound() ? "YES" : "NO",
                  ESP.getPsramSize(),
                  ESP.getFreePsram());
    Serial.printf("POST: efuse_mac=%012llX\n", ESP.getEfuseMac());
    Serial.printf("POST: usb_serial=COM5 baud=115200\n");
    Serial.flush();
}

static void print_post_summary()
{
    Serial.println("==================================================");
    Serial.println(" POST SUMMARY");
    Serial.println("==================================================");
    Serial.printf("POST: software_version  [%s]\n", VST_BASE_SOFTWARE_VERSION);
    Serial.printf("POST: device_name       [%s]\n", g_config.device_name);
    Serial.printf("POST: post_log          [%s]\n", g_config.logging.post_log);
    Serial.printf("POST: image_prefix      [%s]\n", g_config.logging.image_prefix);
    Serial.printf("POST: log_rotation      [every=%u min retention=%u days upload=%s upload_every=%u min max_files=%u min_battery=%u%%]\n",
                  g_config.logging.rotation_interval_minutes,
                  g_config.logging.retention_days,
                  g_config.logging.upload_enabled ? "YES" : "NO",
                  g_config.logging.upload_interval_minutes,
                  g_config.logging.upload_max_files_per_run,
                  g_config.logging.upload_min_battery_percent);
    Serial.printf("POST: features          [gnss_probe=%s ack_frames=%s]\n",
                  g_config.features.gnss_probe ? "YES" : "NO",
                  g_config.features.ack_frames ? "YES" : "NO");
    Serial.printf("POST: stepper_wait_ms   [%u]\n", g_config.stepper.reverse_wait_ms);
    Serial.printf("POST: stepper_direction [%s]\n", g_config.stepper.start_direction);
    Serial.printf("POST: stepper_post_test [%s]\n", g_config.stepper.post_test_enabled ? "YES" : "NO");
    Serial.printf("POST: power_log_every  [%lu seconds]\n", (unsigned long)g_config.power.log_interval_seconds);
    Serial.printf("POST: solar_auto_optimize [%s]\n", g_config.power.solar_auto_optimize ? "YES" : "NO");
    Serial.printf("POST: health_led       [%u]\n", g_config.health.led);
    Serial.printf("POST: modem_mode      [%u] apn=[%s] direct_sms=[%s] apn_autodetect=[%s] apn_test_all=[%s] validate_http_egress=[%s] operator_auto_select=[%s] candidates=[%u] lookup=[%s,%s]\n",
                  g_config.modem.mode,
                  g_config.modem.apn,
                  g_config.modem.direct_sms ? "YES" : "NO",
                  g_config.modem.apn_autodetect ? "YES" : "NO",
                  g_config.modem.apn_test_all ? "YES" : "NO",
                  g_config.modem.validate_http_egress ? "YES" : "NO",
                  g_config.modem.operator_auto_select ? "YES" : "NO",
                  g_config.modem.apn_candidate_count,
                  g_config.modem.lookup_primary,
                  g_config.modem.lookup_secondary);
    Serial.printf("POST: deep_sleep       [%u %02u:00-%02u:00]\n",
                  g_config.power.deep_sleep,
                  g_config.power.deep_sleep_start_hour,
                  g_config.power.deep_sleep_end_hour);
    Serial.printf("POST: low_battery_sleep [threshold=%u%% wake_every=%u min]\n",
                  g_config.power.low_battery_sleep_percent,
                  g_config.power.low_battery_wake_interval_minutes);
    Serial.printf("POST: reboot_schedule  [cron=%s after_deep_sleep=%s]\n",
                  g_config.power.reboot_cron[0] ? g_config.power.reboot_cron : "-",
                  g_config.power.reboot_after_deep_sleep_wakeup ? "YES" : "NO");
    Serial.printf("POST: azure_uploads    [image_runtime_only=YES cooldown=%lu min failure_cooldown=%lu sec runtime_connect_timeout=%u sec photos_prefix=%s logs_prefix=%s log_post_test=%s]\n",
                  (unsigned long)g_config.azure.cooldown_minutes,
                  (unsigned long)g_config.azure.failure_cooldown_seconds,
                  g_config.azure.runtime_connect_timeout_seconds,
                  g_config.azure.photos_prefix,
                  g_config.azure.logs_prefix,
                  g_config.azure.log_post_test_enabled ? "YES" : "NO");
    Serial.printf("POST: inference_filter  [mode=%u class=%d positive>=%.3f doubtful>=%.3f upload_doubtful_to_azure=%s occurrence=%u window=%u sec]\n",
                  g_config.inference.photo_mode,
                  g_config.inference.detected_class,
                  g_config.inference.confidence_threshold,
                  g_config.inference.doubtful_confidence_threshold,
                  g_config.inference.upload_doubtful_to_azure ? "YES" : "NO",
                  g_config.inference.occurrence,
                  g_config.inference.occurrence_window_seconds);
    print_post_line("modem_at", g_post.modem_ready);
    if (g_config.modem.mode == 2)
        print_post_line("modem_ltem", g_post.modem_ltem, g_post.modem_ltem ? "bearer/ip validated" : "attach failed");
    else
        print_post_warn("modem_ltem", g_config.modem.mode == 0 ? "skipped mode=0" : "skipped mode=1");
    if (g_config.modem.mode == 2) {
        if (g_config.modem.validate_http_egress)
            print_post_line("http_egress", g_post.modem_http, g_post.modem_http ? "kpnthings TLS OK" : "kpnthings TLS failed");
        else
            print_post_warn("http_egress", "skipped by config");
    }
    if (g_config.modem.mode == 2)
        print_post_warn("azure_image_upload", "post probe disabled");
    print_post_line("modem_timestamp", g_post.modem_time, g_post.modem_time ? g_timestamp : "no valid network time");
    print_post_line("gnss_timestamp", g_post.gnss_time, g_post.gnss_time ? g_timestamp : "unavailable");
    print_post_line("system_time", g_post.system_time);
    print_post_line("gnss_command", g_post.gnss_ready, g_post.gnss_ready ? "AT+CGNSPWR/AT+CGNSINF" : "unavailable");
    if (g_post.gnss_fix)
        print_post_line("gnss_fix", true, "position fix");
    else
        print_post_warn("gnss_fix", g_gnss.fix ? "raw fix rejected" : "no fix yet");
    if (g_post.gnss_ready) {
        Serial.printf("POST: gnss_powered=%s raw_fix=%s valid=%s utc=%s utc_advancing=%s lat=%s lon=%s sats=%s\n",
                      g_gnss.powered ? "YES" : "NO",
                      g_gnss.fix ? "YES" : "NO",
                      g_gnss.position_valid ? "YES" : "NO",
                      g_gnss.utc[0] ? g_gnss.utc : "-",
                      g_gnss.utc_advancing ? "YES" : "NO",
                      g_gnss.latitude[0] ? g_gnss.latitude : "-",
                      g_gnss.longitude[0] ? g_gnss.longitude : "-",
                      g_gnss.satellites[0] ? g_gnss.satellites : "-");
    }
    print_post_line("gv2_uart", g_post.gv2_uart);
    print_post_line("sd_card", g_post.sd_card);
    print_post_line("sd_config", g_post.sd_config, g_post.sd_config ? "/config.json" : "unavailable");
    print_post_line("power_monitor", g_post.power, g_post.power ? "/power.log" : "unavailable");
    Serial.printf("POST: startup_heap_free=%u\n", ESP.getFreeHeap());
    Serial.println("POST: receiver idle; waiting for GV2 UART traffic");
    Serial.println("==================================================");
    Serial.flush();
}

static void write_post_summary_to_sd()
{
    if (!sdcard_available())
        return;

    String summary = make_post_summary_text();
    bool ok = sdcard_write_log(g_config.logging.post_log, summary);
    print_post_line("sd_post_log", ok, ok ? g_config.logging.post_log : "write failed");
}

static bool is_digit(char c)
{
    return (c >= '0' && c <= '9');
}

static bool parse2(const char *p, int &out)
{
    if (!is_digit(p[0]) || !is_digit(p[1])) return false;
    out = (p[0] - '0') * 10 + (p[1] - '0');
    return true;
}

static bool parse4(const char *p, int &out)
{
    if (!is_digit(p[0]) || !is_digit(p[1]) ||
        !is_digit(p[2]) || !is_digit(p[3])) return false;
    out = (p[0] - '0') * 1000 +
          (p[1] - '0') * 100 +
          (p[2] - '0') * 10 +
          (p[3] - '0');
    return true;
}

/* =========================================================
   SYSTEM TIME SET
   ========================================================= */
static bool set_system_time_from_timestamp(const char *ts)
{
    if (!ts || strlen(ts) != 15 || ts[8] != '_')
        return false;

    int year, mon, day, hour, min, sec;

    if (!parse4(ts + 0, year) ||
        !parse2(ts + 4, mon)  ||
        !parse2(ts + 6, day)  ||
        !parse2(ts + 9, hour) ||
        !parse2(ts + 11, min) ||
        !parse2(ts + 13, sec))
        return false;

    struct tm tm{};
    tm.tm_year = year - 1900;
    tm.tm_mon  = mon - 1;
    tm.tm_mday = day;
    tm.tm_hour = hour;
    tm.tm_min  = min;
    tm.tm_sec  = sec;
    tm.tm_isdst = -1;

    time_t t = mktime(&tm);
    if (t < 0)
        return false;

    struct timeval tv{};
    tv.tv_sec = t;
    tv.tv_usec = 0;
    settimeofday(&tv, nullptr);

    char buf[32];
    strftime(buf, sizeof(buf), "%Y-%m-%d %H:%M:%S", &tm);
    Serial.print("TIME: system time set ");
    Serial.println(buf);

    return true;
}

static bool cron_field_is_wildcard(const char *field)
{
    return !field || strcmp(field, "*") == 0;
}

static bool parse_uint_token(const char *s, int &out)
{
    if (!s || !s[0])
        return false;

    int value = 0;
    for (const char *p = s; *p; p++) {
        if (*p < '0' || *p > '9')
            return false;
        value = value * 10 + (*p - '0');
        if (value > 10000)
            return false;
    }
    out = value;
    return true;
}

static bool cron_single_part_matches(const char *part, int value, int min_value, int max_value, bool day_of_week)
{
    if (!part || !part[0])
        return false;

    if (strcmp(part, "*") == 0)
        return true;

    if (part[0] == '*' && part[1] == '/') {
        int step = 0;
        if (!parse_uint_token(part + 2, step) || step <= 0)
            return false;
        return (value - min_value) % step == 0;
    }

    const char *dash = strchr(part, '-');
    if (dash) {
        char left[8] = {0};
        char right[8] = {0};
        size_t left_len = min<size_t>((size_t)(dash - part), sizeof(left) - 1);
        strlcpy(left, part, left_len + 1);
        strlcpy(right, dash + 1, sizeof(right));

        int start = 0;
        int end = 0;
        if (!parse_uint_token(left, start) || !parse_uint_token(right, end))
            return false;
        if (day_of_week && start == 7)
            start = 0;
        if (day_of_week && end == 7)
            end = 0;
        if (start < min_value || start > max_value || end < min_value || end > max_value)
            return false;
        if (start <= end)
            return value >= start && value <= end;
        return value >= start || value <= end;
    }

    int expected = 0;
    if (!parse_uint_token(part, expected))
        return false;
    if (day_of_week && expected == 7)
        expected = 0;
    return expected >= min_value && expected <= max_value && value == expected;
}

static bool cron_field_matches(const char *field, int value, int min_value, int max_value, bool day_of_week = false)
{
    if (!field || !field[0])
        return false;

    char copy[64] = {0};
    strlcpy(copy, field, sizeof(copy));
    char *ctx = nullptr;
    for (char *part = strtok_r(copy, ",", &ctx); part; part = strtok_r(nullptr, ",", &ctx)) {
        if (cron_single_part_matches(part, value, min_value, max_value, day_of_week))
            return true;
    }
    return false;
}

static bool cron_schedule_matches_now(const char *expr, const struct tm &tm)
{
    if (!expr || !expr[0])
        return false;

    char copy[96] = {0};
    strlcpy(copy, expr, sizeof(copy));
    char *fields[5] = {nullptr, nullptr, nullptr, nullptr, nullptr};
    char *ctx = nullptr;
    uint8_t count = 0;
    for (char *token = strtok_r(copy, " \t", &ctx); token && count < 5; token = strtok_r(nullptr, " \t", &ctx))
        fields[count++] = token;
    if (count != 5)
        return false;

    bool minute = cron_field_matches(fields[0], tm.tm_min, 0, 59);
    bool hour = cron_field_matches(fields[1], tm.tm_hour, 0, 23);
    bool month = cron_field_matches(fields[3], tm.tm_mon + 1, 1, 12);
    bool dom_wild = cron_field_is_wildcard(fields[2]);
    bool dow_wild = cron_field_is_wildcard(fields[4]);
    bool dom = cron_field_matches(fields[2], tm.tm_mday, 1, 31);
    bool dow = cron_field_matches(fields[4], tm.tm_wday, 0, 7, true);
    bool day = (!dom_wild && !dow_wild) ? (dom || dow) : (dom && dow);

    return minute && hour && month && day;
}

static void reboot_now(const char *reason)
{
    Serial.printf("POWER: reboot requested reason=%s\n", reason ? reason : "unknown");
    sdcard_append_log("/power.log", String("{\"event\":\"reboot\",\"device_name\":\"") +
                                      String(g_config.device_name) +
                                      String("\",\"reason\":\"") +
                                      String(reason ? reason : "unknown") +
                                      String("\"}\n"));
    Serial.flush();
    delay(100);
    ESP.restart();
}

static void reboot_after_deep_sleep_wakeup_if_configured()
{
    if (!g_config.power.reboot_after_deep_sleep_wakeup)
        return;
    if (esp_reset_reason() != ESP_RST_DEEPSLEEP)
        return;
    if (g_deep_sleep_reboot_marker != DEEP_SLEEP_REBOOT_MARKER)
        return;

    g_deep_sleep_reboot_marker = 0;
    reboot_now("after_deep_sleep_wakeup");
}

static void reboot_if_cron_matches()
{
    if (!g_config.power.reboot_cron[0])
        return;

    struct tm tm{};
    if (!current_local_time(tm))
        return;

    static int last_reboot_minute_key = -1;
    int minute_key = tm.tm_yday * 24 * 60 + tm.tm_hour * 60 + tm.tm_min;
    if (minute_key == last_reboot_minute_key)
        return;

    if (cron_schedule_matches_now(g_config.power.reboot_cron, tm)) {
        last_reboot_minute_key = minute_key;
        reboot_now("scheduled_cron");
    }
}

static bool gnss_utc_to_timestamp(const char *utc, char *out, size_t out_len)
{
    if (!utc || !out || out_len < 16)
        return false;

    if (strlen(utc) < 14)
        return false;

    for (uint8_t i = 0; i < 14; i++) {
        if (!is_digit(utc[i]))
            return false;
    }

    int year = 0;
    if (!parse4(utc, year) || year < 2020 || year > 2099)
        return false;

    snprintf(out, out_len, "%.8s_%.6s", utc, utc + 8);
    return true;
}

static bool apply_gnss_time_if_usable(const char *phase, bool post_style_log)
{
    if (!g_config.time.allow_gnss_fallback || g_post.system_time)
        return g_post.system_time;

    if (!g_config.features.gnss_probe)
        return false;

    if (g_config.modem.mode == 0 || !g_post.modem_ready)
        return false;

    Serial.printf("%s: GNSS time fallback probe begin\n", phase);
    g_post.gnss_ready = modem_gnss_probe(g_gnss, 10000);
    g_post.gnss_fix = g_gnss.position_valid;

    if (post_style_log) {
        print_post_line("gnss_command", g_post.gnss_ready, g_post.gnss_ready ? "AT+CGNSPWR/AT+CGNSINF" : "unavailable");
        if (g_post.gnss_fix)
            print_post_line("gnss_fix", true, "position fix");
        else
            print_post_warn("gnss_fix", g_gnss.fix ? "raw fix rejected" : "no fix yet");
    }

    char gnss_timestamp[32] = {0};
    bool gnss_time_usable = (g_gnss.position_valid || g_gnss.utc_advancing) &&
                            gnss_utc_to_timestamp(g_gnss.utc, gnss_timestamp, sizeof(gnss_timestamp));
    if (!gnss_time_usable) {
        const char *reason = g_gnss.utc_valid ? "GNSS UTC stale/no fix" : "trusted GNSS time unavailable";
        if (post_style_log)
            print_post_warn("gnss_timestamp", reason);
        else
            Serial.printf("%s: GNSS timestamp unavailable reason=%s\n", phase, reason);
        return false;
    }

    strlcpy(g_timestamp, gnss_timestamp, sizeof(g_timestamp));
    g_post.gnss_time = true;
    g_post.system_time = set_system_time_from_timestamp(g_timestamp);
    if (post_style_log)
        print_post_line("gnss_timestamp", g_post.system_time, g_post.system_time ? g_timestamp : "invalid");
    else
        Serial.printf("%s: GNSS timestamp recovered [%s]\n", phase, g_timestamp);
    return g_post.system_time;
}

struct HealthState {
    bool has_error = false;
    bool no_uart_comm = true;
    bool no_inference_detection = true;
    bool gv2_camera_error = false;
    bool no_sim_connect = false;
    bool no_sd = true;
    bool low_power = false;
    bool power_valid = false;
    PowerSnapshot power;
    uint32_t last_diagnosis_ms = 0;
    uint32_t last_bytes = 0;
    uint32_t last_jpegs = 0;
    uint32_t last_state_frames = 0;
    uint32_t last_heartbeat_frames = 0;
    uint32_t last_error_frames = 0;
};

static HealthState g_health;

static const char *yn(bool value)
{
    return value ? "YES" : "NO";
}

static void append_json_string(String &s, const char *name, const char *value)
{
    s += "\"";
    s += name;
    s += "\":\"";
    if (value) {
        for (const char *p = value; *p; p++) {
            if (*p == '"' || *p == '\\')
                s += '\\';
            s += *p;
        }
    }
    s += "\"";
}

static void append_json_bool(String &s, const char *name, bool value)
{
    s += "\"";
    s += name;
    s += "\":";
    s += value ? "true" : "false";
}

static bool modem_health_ok()
{
    if (g_config.modem.mode == 0)
        return true;
    if (g_post.modem_powered_down && !g_config.modem.keep_alive_after_post)
        return true;
    if (!g_post.modem_ready)
        return false;
    if (g_config.modem.mode == 1)
        return g_post.modem_network && g_post.modem_time && g_post.system_time;
    return g_post.modem_network && g_post.modem_ltem;
}

static void refresh_modem_health()
{
    if (g_config.modem.mode == 0)
        return;
    if (g_post.modem_powered_down && !g_config.modem.keep_alive_after_post)
        return;

    if (!g_post.modem_ready) {
        Serial.println("MODEM: health recovery init begin");
        g_post.modem_ready = modem_init_early(g_config.modem.operator_auto_select,
                                              g_config.modem.preferred_radio_mode);
        if (!g_post.modem_ready)
            return;
    }

    uint32_t network_timeout_ms = (uint32_t)g_config.time.network_timeout_seconds * 1000UL;
    if (network_timeout_ms == 0)
        network_timeout_ms = 10000UL;

    bool registered = modem_check_network_registered(min<uint32_t>(network_timeout_ms, 5000UL));
    if (!registered) {
        Serial.println("MODEM: health network registration timeout");
        if (!modem_at_responsive(1000)) {
            Serial.println("MODEM: health modem unresponsive; skipping detailed diagnostics and GNSS fallback");
            g_post.modem_ready = false;
            g_post.modem_network = false;
            g_post.modem_ltem = false;
            g_post.modem_time = false;
            return;
        }

        modem_print_sim_network_status();
        if (g_post.modem_network) {
            Serial.println("MODEM: health network registration LOST");
            g_post.modem_time = false;
        }
        g_post.modem_network = false;
        if (!g_post.system_time)
            apply_gnss_time_if_usable("HEALTH", false);
        return;
    }

    bool network_recovered = !g_post.modem_network;
    if (network_recovered)
        Serial.println("MODEM: health network registration OK");
    g_post.modem_network = true;

    if (g_config.modem.mode == 1 && (network_recovered || !g_post.modem_time || !g_post.system_time)) {
        Serial.println("MODEM: health timestamp retry begin");
        if (modem_get_timestamp(g_timestamp, sizeof(g_timestamp), network_timeout_ms)) {
            g_post.modem_time = true;
            g_post.system_time = set_system_time_from_timestamp(g_timestamp);
            Serial.printf("MODEM: health timestamp recovered [%s]\n", g_timestamp);
        } else if (network_recovered) {
            g_post.modem_time = false;
            Serial.println("MODEM: health timestamp recovery FAILED");
        }
    } else if (g_config.modem.mode == 2 && !g_post.modem_ltem) {
        Serial.println("MODEM: health LTE-M retry begin");
        g_post.modem_ltem = modem_validate_ltem_apn_candidates(g_config.modem,
                                                               network_timeout_ms);
    }

    if (!g_post.system_time)
        apply_gnss_time_if_usable("HEALTH", false);
}

static void append_health_errors_json(String &s)
{
    bool first = true;
    auto add_error = [&](const char *name) {
        if (!first)
            s += ",";
        s += "\"";
        for (const char *p = name; *p; p++) {
            if (*p == '"' || *p == '\\')
                s += '\\';
            s += *p;
        }
        s += "\"";
        first = false;
    };

    s += "\"errors\":[";
    if (g_health.no_uart_comm)
        add_error("no_uart_comm");
    if (g_health.no_inference_detection)
        add_error("no_inference_detection");
    if (g_health.gv2_camera_error)
        add_error("gv2_camera_error");
    if (g_health.no_sim_connect)
        add_error("no_sim_connect");
    if (g_health.no_sd)
        add_error("no_sd");
    if (g_health.low_power)
        add_error("low_power");
    s += "]";
}

static String make_health_log_line(uint32_t now,
                                   uint32_t delta_bytes,
                                   uint32_t delta_jpegs,
                                   uint32_t delta_state,
                                   uint32_t delta_heartbeats,
                                   uint32_t delta_errors,
                                   const Gv2UartStats &uart_stats)
{
    String s;
    s.reserve(1500);
    String timestamp_iso = current_timestamp_iso();
    String timestamp_compact = current_timestamp_compact();
    s += "{";
    append_json_string(s, "type", "health");
    s += ",";
    append_json_string(s, "device_name", g_config.device_name);
    s += ",";
    append_json_string(s, "timestamp", timestamp_iso.c_str());
    s += ",\"uptime_ms\":";
    s += (unsigned long)now;
    s += ",";
    append_json_string(s, "state", g_health.has_error ? "ERROR" : "OK");
    s += ",";
    append_health_errors_json(s);
    s += ",\"delta\":{\"gv2_bytes\":";
    s += (unsigned long)delta_bytes;
    s += ",\"gv2_jpegs\":";
    s += (unsigned long)delta_jpegs;
    s += ",\"gv2_state\":";
    s += (unsigned long)delta_state;
    s += ",\"gv2_heartbeats\":";
    s += (unsigned long)delta_heartbeats;
    s += ",\"gv2_errors\":";
    s += (unsigned long)delta_errors;
    s += "},\"gv2\":{\"bytes\":";
    s += (unsigned long)uart_stats.bytes;
    s += ",\"jpegs\":";
    s += (unsigned long)uart_stats.jpeg_frames;
    s += ",\"state_frames\":";
    s += (unsigned long)uart_stats.state_frames;
    s += ",\"heartbeats\":";
    s += (unsigned long)uart_stats.heartbeat_frames;
    s += ",\"heartbeat_status\":";
    s += (unsigned)uart_stats.last_heartbeat_status;
    s += ",\"heartbeat_counter\":";
    s += (unsigned long)uart_stats.last_heartbeat_counter;
    s += ",\"errors\":";
    s += (unsigned long)uart_stats.error_frames;
    s += ",\"last_error_code\":";
    s += (unsigned)uart_stats.last_error_code;
    s += ",\"last_error_detail\":";
    s += (unsigned)uart_stats.last_error_detail;
    s += "},\"modem\":{";
    append_json_bool(s, "ok", modem_health_ok());
    s += ",\"mode\":";
    s += (unsigned)g_config.modem.mode;
    s += ",";
    append_json_bool(s, "at", g_post.modem_ready);
    s += ",";
    append_json_bool(s, "network", g_post.modem_network);
    s += ",";
    append_json_bool(s, "ltem", g_post.modem_ltem);
    s += ",";
    append_json_bool(s, "time", g_post.modem_time);
    s += "},\"time\":{";
    append_json_bool(s, "system", g_post.system_time);
    s += ",";
    append_json_string(s, "compact", timestamp_compact.c_str());
    s += "},\"gnss\":{";
    append_json_bool(s, "ok", g_post.gnss_ready);
    s += ",";
    append_json_bool(s, "fix", g_post.gnss_fix);
    s += ",";
    append_json_bool(s, "utc_advancing", g_gnss.utc_advancing);
    s += ",";
    append_json_string(s, "utc", g_gnss.utc);
    s += "},\"io\":{";
    append_json_bool(s, "uart", g_post.gv2_uart);
    s += ",";
    append_json_bool(s, "sd", sdcard_available());
    s += ",\"health_led\":";
    s += (unsigned)g_config.health.led;
    s += "},\"power\":{";
    append_json_bool(s, "valid", g_health.power_valid);
    s += ",";
    append_json_bool(s, "low_power", g_health.low_power);
    s += ",\"battery_percent\":";
    s += g_health.power_valid ? g_health.power.battery_percent : -1;
    s += ",\"battery_mv\":";
    s += g_health.power_valid ? (unsigned)g_health.power.battery_mv : 0;
    s += ",\"vbus_mv\":";
    s += g_health.power_valid ? (unsigned)g_health.power.vbus_mv : 0;
    s += ",";
    append_json_bool(s, "mains_power", g_health.power_valid && g_health.power.mains_power_present);
    s += ",";
    append_json_bool(s, "solar_suspect", g_health.power_valid && g_health.power.solar_suspect);
    s += ",";
    append_json_bool(s, "battery_rising_no_vbus", g_health.power_valid && g_health.power.battery_rising_no_vbus);
    s += "},\"heap_free\":";
    s += ESP.getFreeHeap();
    s += "}\n";
    return s;
}

static bool diagnose_and_print_health()
{
    static uint32_t last_ms = 0;
    static uint8_t gv2_uart_recovery_attempts = 0;
    uint32_t now = millis();
    constexpr uint32_t interval_ms = 60000UL;

    if (last_ms == 0) {
        last_ms = now;
        return false;
    }

    if (now - last_ms < interval_ms)
        return false;

    last_ms = now;

    const Gv2UartStats &uart_stats = gv2_uart_stats();
    uint32_t delta_bytes = uart_stats.bytes - g_health.last_bytes;
    uint32_t delta_jpegs = uart_stats.jpeg_frames - g_health.last_jpegs;
    uint32_t delta_state = uart_stats.state_frames - g_health.last_state_frames;
    uint32_t delta_heartbeats = uart_stats.heartbeat_frames - g_health.last_heartbeat_frames;
    uint32_t delta_errors = uart_stats.error_frames - g_health.last_error_frames;

    if (uart_stats.camera_error_active && delta_errors == 0 && (delta_jpegs > 0 || delta_state > 0 || delta_heartbeats > 0)) {
        gv2_uart_clear_camera_error();
        Serial.println("HEALTH: gv2_camera_error cleared by recovered GV2 traffic");
    }

    refresh_modem_health();

    g_health.no_uart_comm = !g_post.gv2_uart || delta_bytes == 0;
    if (g_health.no_uart_comm && g_post.gv2_uart && gv2_uart_recovery_attempts < 3) {
        gv2_uart_recovery_attempts++;
        Serial.printf("HEALTH: GV2 UART recovery attempt=%u reason=no_uart_comm\n",
                      (unsigned)gv2_uart_recovery_attempts);
        g_post.gv2_uart = gv2_uart_recover(g_config.uart);
    } else if (!g_health.no_uart_comm && gv2_uart_recovery_attempts != 0) {
        Serial.println("HEALTH: GV2 UART recovery cleared by traffic");
        gv2_uart_recovery_attempts = 0;
    }
    g_health.no_inference_detection = !g_health.no_uart_comm &&
                                      delta_jpegs == 0 &&
                                      delta_heartbeats == 0 &&
                                      delta_state == 0;
    g_health.gv2_camera_error = uart_stats.camera_error_active;
    g_health.no_sim_connect = !modem_health_ok();
    g_health.no_sd = !sdcard_available();
    g_health.power_valid = power_read_snapshot(g_health.power);
    g_health.low_power = false;
    if (g_health.power_valid) {
        g_health.low_power = g_health.power.battery_present &&
                             !g_health.power.mains_power_present &&
                             ((g_health.power.battery_percent >= 0 && g_health.power.battery_percent <= 20) ||
                              (g_health.power.battery_mv > 0 && g_health.power.battery_mv < 3500));
    }

    g_health.has_error = g_health.no_uart_comm ||
                         g_health.no_inference_detection ||
                         g_health.gv2_camera_error ||
                         g_health.no_sim_connect ||
                         g_health.no_sd ||
                         g_health.low_power;
    g_health.last_diagnosis_ms = now;
    g_health.last_bytes = uart_stats.bytes;
    g_health.last_jpegs = uart_stats.jpeg_frames;
    g_health.last_state_frames = uart_stats.state_frames;
    g_health.last_heartbeat_frames = uart_stats.heartbeat_frames;
    g_health.last_error_frames = uart_stats.error_frames;

    Serial.printf("HEALTH: ms=%lu state=%s errors=%s%s%s%s%s%s gv2_delta_bytes=%lu gv2_delta_jpegs=%lu gv2_delta_state=%lu gv2_delta_heartbeats=%lu gv2_delta_errors=%lu battery_pct=%d battery_mv=%u mains_power=%s vbus_mv=%u solar=%s\n",
                  (unsigned long)now,
                  g_health.has_error ? "ERROR" : "OK",
                  g_health.no_uart_comm ? " no_uart_comm" : "",
                  g_health.no_inference_detection ? " no_inference_detection" : "",
                  g_health.gv2_camera_error ? " gv2_camera_error" : "",
                  g_health.no_sim_connect ? " no_sim_connect" : "",
                  g_health.no_sd ? " no_sd" : "",
                  g_health.low_power ? " low_power" : "",
                  (unsigned long)delta_bytes,
                  (unsigned long)delta_jpegs,
                  (unsigned long)delta_state,
                  (unsigned long)delta_heartbeats,
                  (unsigned long)delta_errors,
                  g_health.power_valid ? g_health.power.battery_percent : -1,
                  g_health.power_valid ? (unsigned)g_health.power.battery_mv : 0,
                  (g_health.power_valid && g_health.power.mains_power_present) ? "YES" : "NO",
                  g_health.power_valid ? (unsigned)g_health.power.vbus_mv : 0,
                  (g_health.power_valid && g_health.power.solar_suspect) ? "SUSPECT" : "NO");

    String heartbeat_time = current_timestamp_compact();
    Serial.printf("HEARTBEAT: build=post-log-v2 ms=%lu gv2_bytes=%lu gv2_jpegs=%lu gv2_state=%lu gv2_heartbeats=%lu gv2_heartbeat_status=%u/%lu gv2_errors=%lu gv2_last_error=%u/%u heap=%u modem=%s time=%s gnss=%s fix=%s uart=%s sd=%s health=%s low_power=%s mains_power=%s solar=%s\n",
                  (unsigned long)now,
                  (unsigned long)uart_stats.bytes,
                  (unsigned long)uart_stats.jpeg_frames,
                  (unsigned long)uart_stats.state_frames,
                  (unsigned long)uart_stats.heartbeat_frames,
                  (unsigned)uart_stats.last_heartbeat_status,
                  (unsigned long)uart_stats.last_heartbeat_counter,
                  (unsigned long)uart_stats.error_frames,
                  (unsigned)uart_stats.last_error_code,
                  (unsigned)uart_stats.last_error_detail,
                  ESP.getFreeHeap(),
                  modem_health_ok() ? "OK" : "NO",
                  heartbeat_time.length() > 0 ? heartbeat_time.c_str() : "NO",
                  g_post.gnss_ready ? "OK" : "NO",
                  g_post.gnss_fix ? "YES" : "NO",
                  g_post.gv2_uart ? "OK" : "NO",
                  sdcard_available() ? "OK" : "NO",
                  g_health.has_error ? "ERROR" : "OK",
                  yn(g_health.low_power),
                  (g_health.power_valid && g_health.power.mains_power_present) ? "YES" : "NO",
                  (g_health.power_valid && g_health.power.solar_suspect) ? "SUSPECT" : "NO");
    sdcard_append_log("/health.log",
                      make_health_log_line(now,
                                           delta_bytes,
                                           delta_jpegs,
                                           delta_state,
                                           delta_heartbeats,
                                           delta_errors,
                                           uart_stats));
    Serial.flush();
    return true;
}

static void print_power_after_heartbeat()
{
    power_log_snapshot_when_due();
}

static void poll_status_led()
{
    static bool led_on = false;
    static uint32_t cycle_start_ms = 0;
    static bool last_error_state = false;
    static uint32_t last_power_check_ms = 0;
    static bool usb_power_present = false;

    uint32_t now = millis();
    if (last_power_check_ms == 0 || now - last_power_check_ms >= 1000UL) {
        PowerSnapshot snapshot;
        usb_power_present = power_read_snapshot(snapshot) && snapshot.mains_power_present;
        last_power_check_ms = now;
    }

    if (g_config.health.led == 0 || !usb_power_present) {
        if (led_on) {
            led_on = false;
            stepper_set_status_led(false);
        }
        return;
    }

    bool error_state = g_health.has_error;
    if (cycle_start_ms == 0 || error_state != last_error_state || now - cycle_start_ms >= 10000UL) {
        cycle_start_ms = now;
        last_error_state = error_state;
    }

    uint32_t phase = now - cycle_start_ms;
    bool desired = false;

    if (!error_state) {
        desired = phase < 500UL;
    } else {
        desired = (phase < 120UL) ||
                  (phase >= 240UL && phase < 360UL) ||
                  (phase >= 480UL && phase < 600UL);
    }

    if (desired != led_on) {
        led_on = desired;
        stepper_set_status_led(led_on);
    }
}

/* =========================================================
   SETUP
   ========================================================= */
void setup()
{
    Serial.begin(115200);
    wait_for_serial(8000);
    delay(2000);

    print_system_info();
    stepper_run_post_start_led_signal();

    Serial.println("POST: SD card init begin");
    g_post.sd_card = sdcard_init();
    print_post_line("sd_card", g_post.sd_card);
    g_post.sd_config = sdcard_ensure_config();
    print_post_line("sd_config", g_post.sd_config, g_post.sd_config ? "/config.json" : "unavailable");
    bool config_loaded = sdcard_load_config(g_config);
    print_post_line("config_load", config_loaded, config_loaded ? "loaded" : "defaults");
    sdcard_set_logging_policy(g_config.logging);
    power_set_device_name(g_config.device_name);
    modem_set_device_name(g_config.device_name);
    reboot_after_deep_sleep_wakeup_if_configured();

    g_post.power = power_init(g_config.power);
    print_post_line("power_monitor", g_post.power, g_post.power ? "/power.log" : "unavailable");
    sleep_if_battery_too_low("post_power_check");

    if (g_config.modem.mode == 0) {
        Serial.println("POST: modem skipped by config mode=0 (no SIM/no modem)");
        print_post_warn("modem_at", "skipped mode=0");
        print_post_warn("modem_timestamp", "skipped mode=0");
        print_post_warn("gnss_command", "skipped mode=0");
    } else {
        Serial.printf("POST: modem init begin mode=%u\n", g_config.modem.mode);
        if (g_config.modem.mode == 1 && g_config.modem.apn_autodetect) {
            Serial.println("POST: APN autodetect skipped in modem mode=1; set modem.mode=2 for LTE-M/APN probing");
            sdcard_append_log("/health.log", String("{\"type\":\"modem_apn_probe\",\"device_name\":\"") +
                                          String(g_config.device_name) +
                                          String("\",\"event\":\"skipped\",\"result\":\"skipped\",\"detail\":\"mode_1_time_only_set_mode_2_for_apn_probe\"}\n"));
        }
    }

    if (g_config.modem.mode != 0 &&
        modem_init_early(g_config.modem.operator_auto_select,
                         g_config.modem.preferred_radio_mode)) {
        g_post.modem_ready = true;
        print_post_line("modem_at", true);

        uint32_t network_timeout_ms = (uint32_t)g_config.time.network_timeout_seconds * 1000UL;
        if (g_config.modem.mode == 2) {
            Serial.println("POST: LTE-M validation begin");
            g_post.modem_ltem = modem_validate_ltem_apn_candidates(g_config.modem,
                                                                   network_timeout_ms);
            g_post.modem_network = g_post.modem_ltem;
            print_post_line("modem_ltem", g_post.modem_ltem, g_post.modem_ltem ? "bearer/ip validated" : "attach failed");
            if (g_post.modem_ltem) {
                g_post.modem_http = g_config.modem.validate_http_egress;
                if (g_config.modem.validate_http_egress)
                    print_post_line("http_egress", true, "validated during LTE-M probe");
                else
                    print_post_warn("http_egress", "skipped by config");
            }
        }

        bool should_query_modem_time = g_config.modem.mode == 1 ||
                                       (g_config.modem.mode == 2 && g_post.modem_ltem);
        if (should_query_modem_time) {
            Serial.println("POST: modem timestamp begin; waiting for network time");
            if (modem_get_timestamp(g_timestamp, sizeof(g_timestamp), network_timeout_ms)) {
                g_post.modem_network = true;
                g_post.modem_time = true;
                Serial.printf("POST: modem_timestamp [%s]\n", g_timestamp);
                g_post.system_time = set_system_time_from_timestamp(g_timestamp);
                print_post_line("system_time", g_post.system_time);
            } else {
                print_post_line("modem_timestamp", false, "unavailable");
            }
        } else {
            print_post_warn("modem_timestamp", "skipped; LTE-M unavailable");
        }

        if (g_config.modem.mode == 2)
            print_post_warn("azure_image_upload", g_post.modem_ltem ? "post probe disabled" : "skipped; LTE-M unavailable");

        if (g_config.modem.mode != 0)
            send_post_sms_probe();

        bool should_probe_gnss = g_config.features.gnss_probe &&
                                 (g_config.modem.mode == 2 ||
                                  (!g_post.system_time && g_config.time.allow_gnss_fallback));
        if (should_probe_gnss) {
            Serial.println("POST: GNSS probe begin; sampling up to 10 seconds for fix");
            g_post.gnss_ready = modem_gnss_probe(g_gnss, 10000);
            g_post.gnss_fix = g_gnss.position_valid;
            print_post_line("gnss_command", g_post.gnss_ready, g_post.gnss_ready ? "AT+CGNSPWR/AT+CGNSINF" : "unavailable");
            if (g_post.gnss_fix)
                print_post_line("gnss_fix", true, "position fix");
            else
                print_post_warn("gnss_fix", g_gnss.fix ? "raw fix rejected" : "no fix yet");
        } else {
            print_post_warn("gnss_command", "skipped mode=1");
        }

        if (!g_post.system_time && g_config.time.allow_gnss_fallback) {
            char gnss_timestamp[32] = {0};
            bool gnss_time_usable = (g_gnss.position_valid || g_gnss.utc_advancing) &&
                                    gnss_utc_to_timestamp(g_gnss.utc, gnss_timestamp, sizeof(gnss_timestamp));
            if (gnss_time_usable) {
                strlcpy(g_timestamp, gnss_timestamp, sizeof(g_timestamp));
                g_post.gnss_time = true;
                g_post.system_time = set_system_time_from_timestamp(g_timestamp);
                print_post_line("gnss_timestamp", g_post.system_time, g_post.system_time ? g_timestamp : "invalid");
            } else {
                print_post_warn("gnss_timestamp", g_gnss.utc_valid ? "GNSS UTC stale/no fix" : "trusted GNSS time unavailable");
            }
        }

        run_log_upload_post_test();

        if (!g_config.modem.keep_alive_after_post) {
            modem_power_down_runtime("post_complete");
            g_post.modem_powered_down = true;
        }
    } else if (g_config.modem.mode != 0) {
        print_post_line("modem_at", false);
    }
    Serial.flush();

    sleep_if_in_configured_window("post_time_sync");

    bool web_started = web_init(g_config.web);
    print_post_line("web_service", web_started, web_started ? "http port 80" : "disabled/unavailable");

    stepper_init(g_config.stepper);
    if (g_config.stepper.post_test_enabled) {
        stepper_run_post_test_cycle();
    } else {
        Serial.println("STEPPER: POST test cycle skipped by config");
    }

    gv2_power_reset_cycle(1000, 0);
    g_post.gv2_uart = gv2_uart_init(g_config.uart);
    gv2_uart_set_log_context(&g_config, &g_gnss);
    print_post_line("gv2_uart", g_post.gv2_uart);

    write_post_summary_to_sd();
    print_post_summary();
}

/* =========================================================
   LOOP
   ========================================================= */
void loop()
{
    sleep_if_battery_too_low("loop");
    sleep_if_in_configured_window("loop");
    reboot_if_cron_matches();
    gv2_uart_poll();
    web_loop();
    poll_status_led();
    if (diagnose_and_print_health())
        print_power_after_heartbeat();
    maybe_upload_rotated_logs();
}
