aggerritsen/VespaSmartTrap-BASE/t-sim/firmware/src/uart.h

#pragma once

#include <Arduino.h>
#include "sdcard.h"
#include "modem.h"

struct Gv2UartStats {
    uint32_t bytes = 0;
    uint32_t state_frames = 0;
    uint32_t heartbeat_frames = 0;
    uint32_t jpeg_frames = 0;
    uint32_t error_frames = 0;
    uint32_t jpeg_invalid = 0;
    uint32_t last_frame_len = 0;
    uint8_t last_state = 0;
    uint8_t last_heartbeat_status = 0;
    uint32_t last_heartbeat_counter = 0;
    uint8_t last_error_code = 0;
    uint8_t last_error_detail = 0;
    uint32_t last_error_counter = 0;
    bool camera_error_active = false;
    uint8_t last_class_idx = 0;
    uint8_t last_conf_u8 = 0;
    uint16_t last_bbox_x = 0;
    uint16_t last_bbox_y = 0;
    uint16_t last_bbox_w = 0;
    uint16_t last_bbox_h = 0;
};

bool gv2_uart_init(const UartConfig &config);
bool gv2_uart_recover(const UartConfig &config);
void gv2_uart_set_log_context(const BaseConfig *config, const ModemGnssInfo *gnss);
void gv2_power_on();
void gv2_power_reset_cycle(uint32_t off_ms = 1000, uint32_t settle_ms = 10000);
void gv2_prepare_for_sleep(const UartConfig &config);
void gv2_uart_poll();
const Gv2UartStats &gv2_uart_stats();
void gv2_uart_clear_camera_error();
